teufelaudio/mynd-hardware/PCB_Schematics/KiCad/Jack_USB/ALTIUM_EMBEDDED_MODELS/SCM7060.step

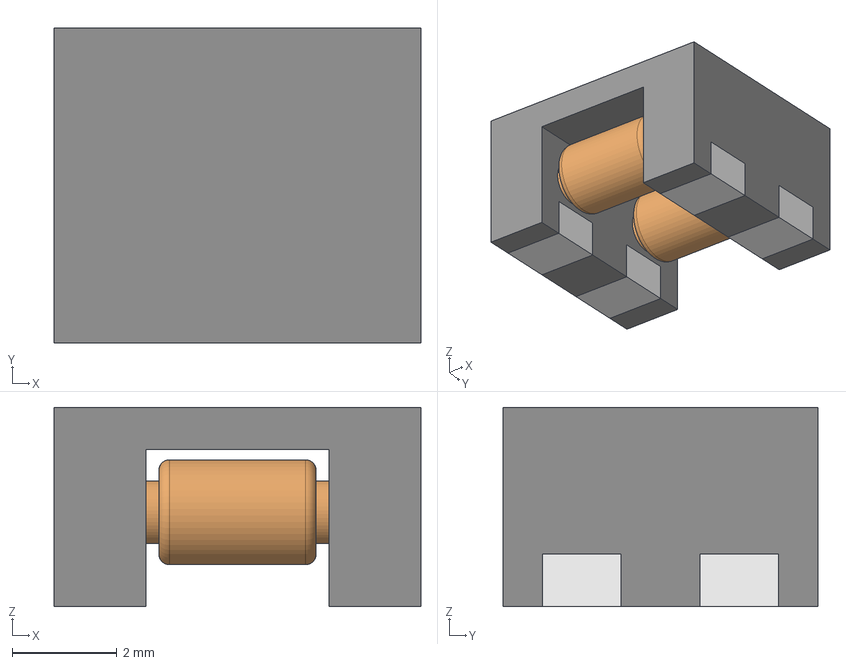
[picture p15: CAD file, 2025-11-21]
PCB_Schematics/KiCad/Jack_USB/ALTIUM_EMBEDDED_MODELS/SCM7060.step
7.00 x 6.00 x 3.80 mm
PIN001
PIN002
PIN003
PIN004
