teufelaudio/mynd-hardware/PCB_Schematics/Altium/Main/ALTIUM_EMBEDDED_MODELS/User Library-RESC1005X___.step

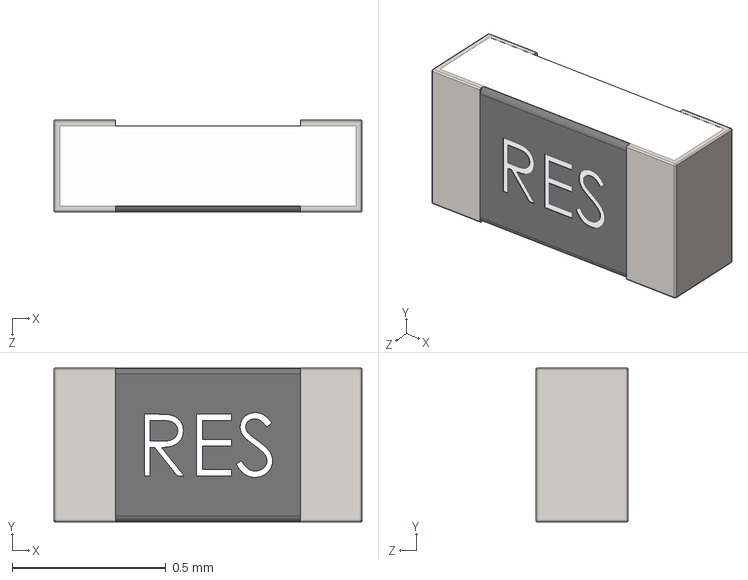
[picture p16: CAD file, 2025-11-21]
PCB_Schematics/Altium/Main/ALTIUM_EMBEDDED_MODELS/User Library-RESC1005X___.step
1.00 x 0.5 x 0.3 mm
