teufelaudio/mynd-hardware/PCB_Schematics/KiCad/Amp/ALTIUM_EMBEDDED_MODELS/RHB0032E.stp

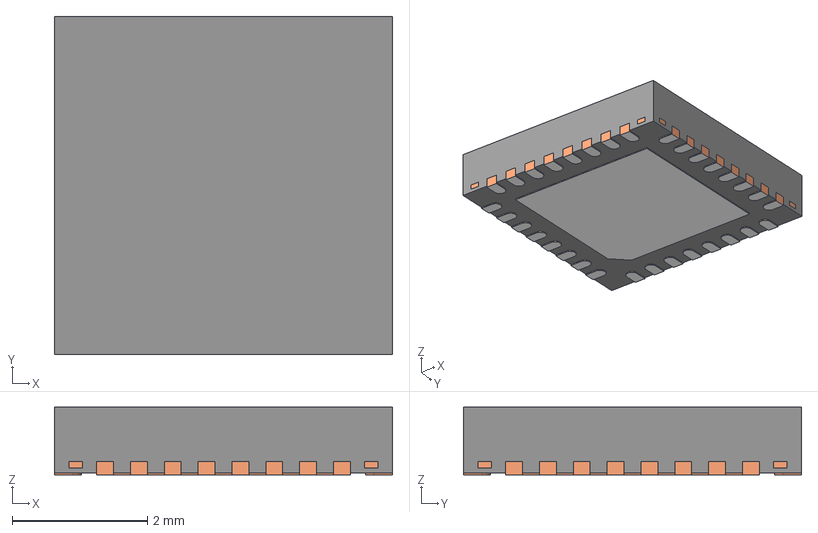
[picture p17: CAD file, 2025-11-21]
PCB_Schematics/KiCad/Amp/ALTIUM_EMBEDDED_MODELS/RHB0032E.stp
5.00 x 5.00 x 1.00 mm
BODY-QFN
FRAME-RHB0032E
PIN1-ID
