teufelaudio/mynd-hardware/PCB_Schematics/KiCad/Bluetooth/ALTIUM_EMBEDDED_MODELS/WB2835P.step

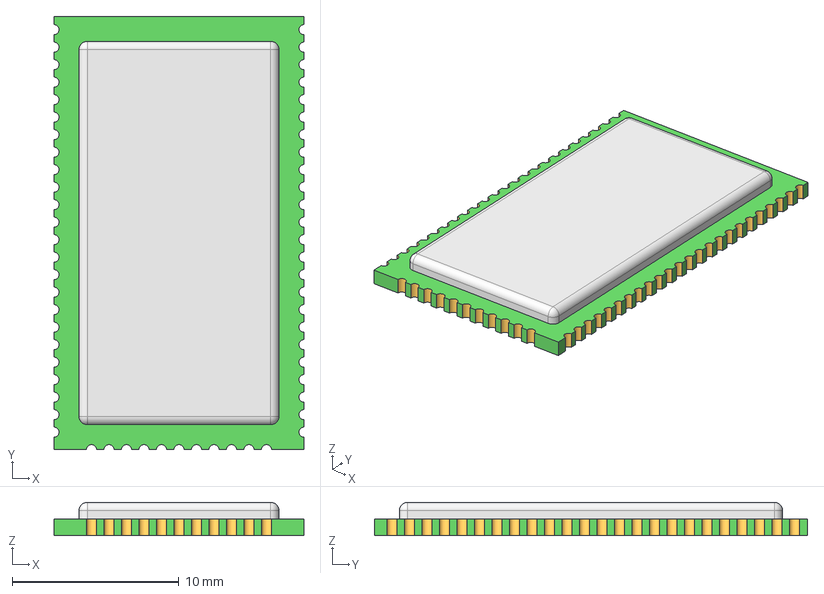
[picture p18: CAD file, 2025-11-21]
PCB_Schematics/KiCad/Bluetooth/ALTIUM_EMBEDDED_MODELS/WB2835P.step
15.0 x 26.0 x 2.00 mm
