teufelaudio/mynd-hardware/PCB_Schematics/KiCad/Jack_USB/ALTIUM_EMBEDDED_MODELS/K3D-DX07WH24JA3-V2_JAE_Proprietary.STEP

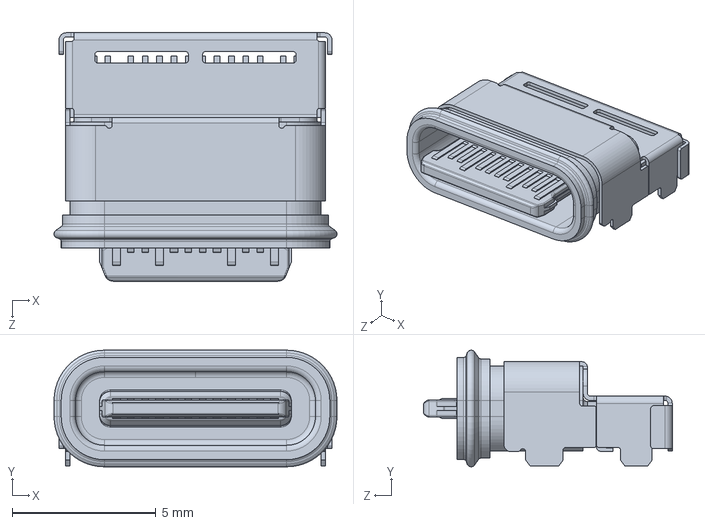
[picture p19: CAD file, 2025-11-21]
PCB_Schematics/KiCad/Jack_USB/ALTIUM_EMBEDDED_MODELS/K3D-DX07WH24JA3-V2_JAE_Proprietary.STEP
9.85 x 4.06 x 8.65 mm
