teufelaudio/mynd-hardware/PCB_Schematics/KiCad/Main/ALTIUM_EMBEDDED_MODELS/User Library-RESC3216X___.step

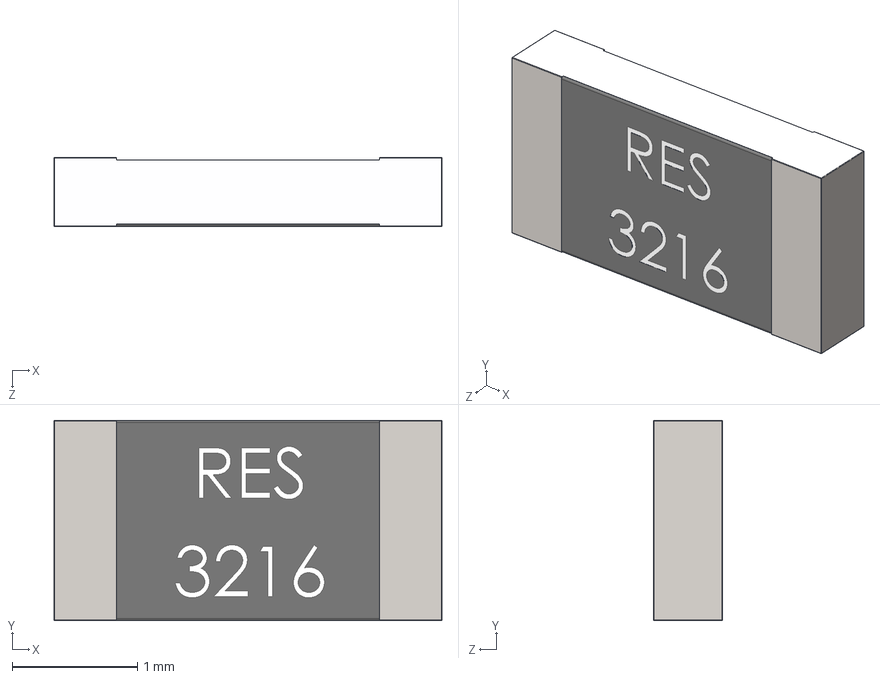
[picture p20: CAD file, 2025-11-21]
PCB_Schematics/KiCad/Main/ALTIUM_EMBEDDED_MODELS/User Library-RESC3216X___.step
3.10 x 1.60 x 0.55 mm
