teufelaudio/mynd-hardware/PCB_Schematics/Altium/Main/ALTIUM_EMBEDDED_MODELS/0805_145.step

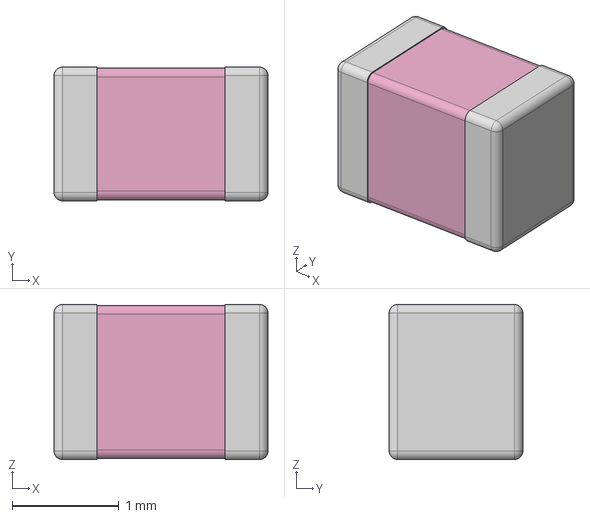
[picture p21: CAD file, 2025-11-21]
PCB_Schematics/Altium/Main/ALTIUM_EMBEDDED_MODELS/0805_145.step
2.00 x 1.25 x 1.45 mm
