teufelaudio/mynd-hardware/PCB_Schematics/KiCad/Amp/ALTIUM_EMBEDDED_MODELS/User Library-CAPC3216X___.step

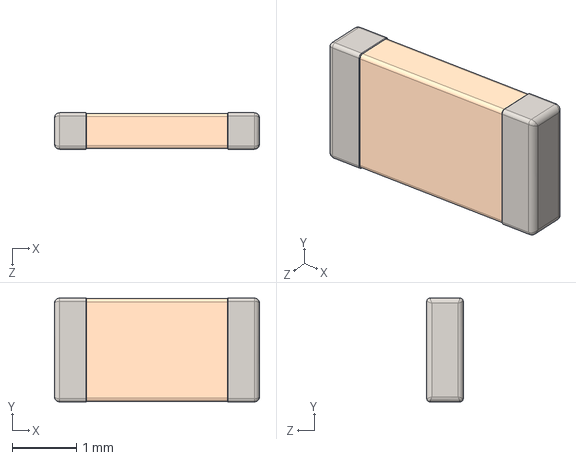
[picture p22: CAD file, 2025-11-21]
PCB_Schematics/KiCad/Amp/ALTIUM_EMBEDDED_MODELS/User Library-CAPC3216X___.step
3.20 x 1.62 x 0.57 mm
