teufelaudio/mynd-hardware/PCB_Schematics/KiCad/Bluetooth/ALTIUM_EMBEDDED_MODELS/User Library-RESC2012X___.STEP

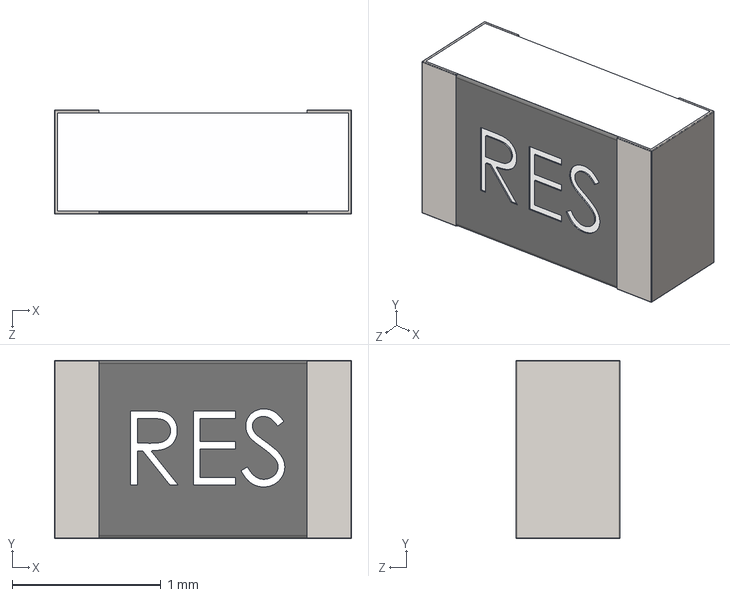
[picture p23: CAD file, 2025-11-21]
PCB_Schematics/KiCad/Bluetooth/ALTIUM_EMBEDDED_MODELS/User Library-RESC2012X___.STEP
2.00 x 1.20 x 0.7 mm
