teufelaudio/mynd-hardware/PCB_Schematics/KiCad/Main/ALTIUM_EMBEDDED_MODELS/pin_header_a-sl127-dg-g10mp1.stp

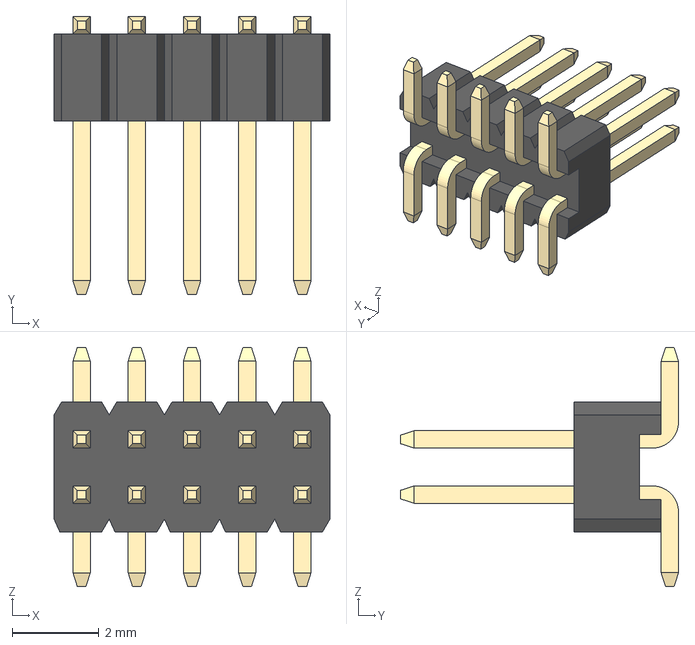
[picture p24: CAD file, 2025-11-21]
PCB_Schematics/KiCad/Main/ALTIUM_EMBEDDED_MODELS/pin_header_a-sl127-dg-g10mp1.stp
6.35 x 6.40 x 5.50 mm
