teufelaudio/mynd-hardware/PCB_Schematics/Altium/Main/ALTIUM_EMBEDDED_MODELS/DBV0003A.stp

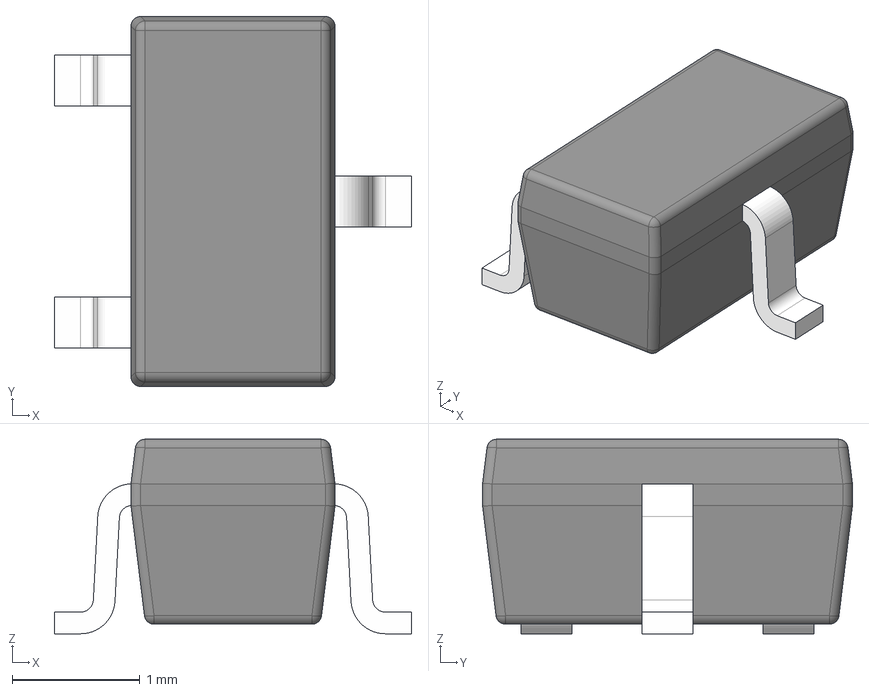
[picture p25: CAD file, 2025-11-21]
PCB_Schematics/Altium/Main/ALTIUM_EMBEDDED_MODELS/DBV0003A.stp
2.80 x 2.90 x 1.52 mm
LEAD x 3
