teufelaudio/mynd-hardware/PCB_Schematics/KiCad/Amp/ALTIUM_EMBEDDED_MODELS/User Library-RESC1608X___.STEP

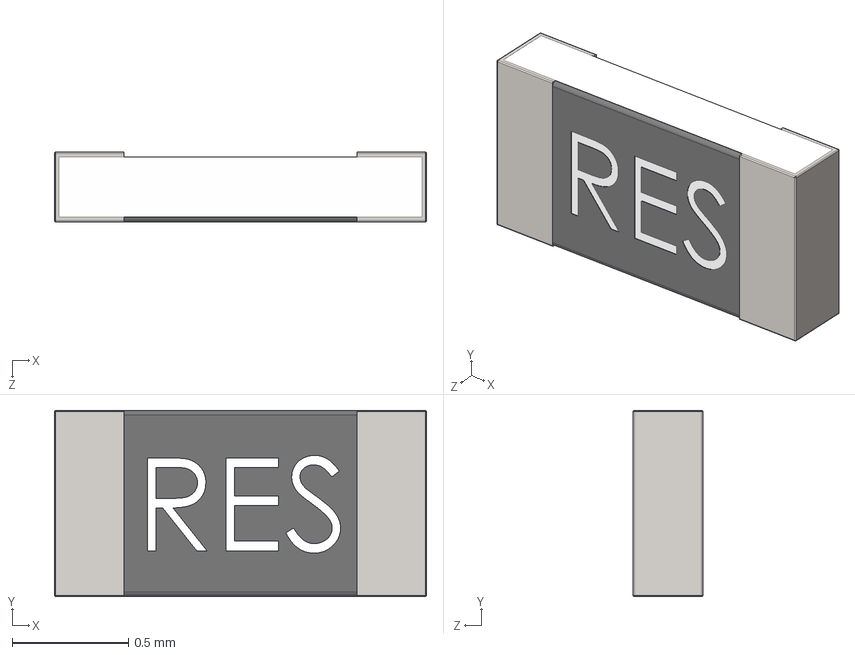
[picture p26: CAD file, 2025-11-21]
PCB_Schematics/KiCad/Amp/ALTIUM_EMBEDDED_MODELS/User Library-RESC1608X___.STEP
1.60 x 0.8 x 0.3 mm
