teufelaudio/mynd-hardware/PCB_Schematics/KiCad/Bluetooth/ALTIUM_EMBEDDED_MODELS/User Library-IPEX.STEP

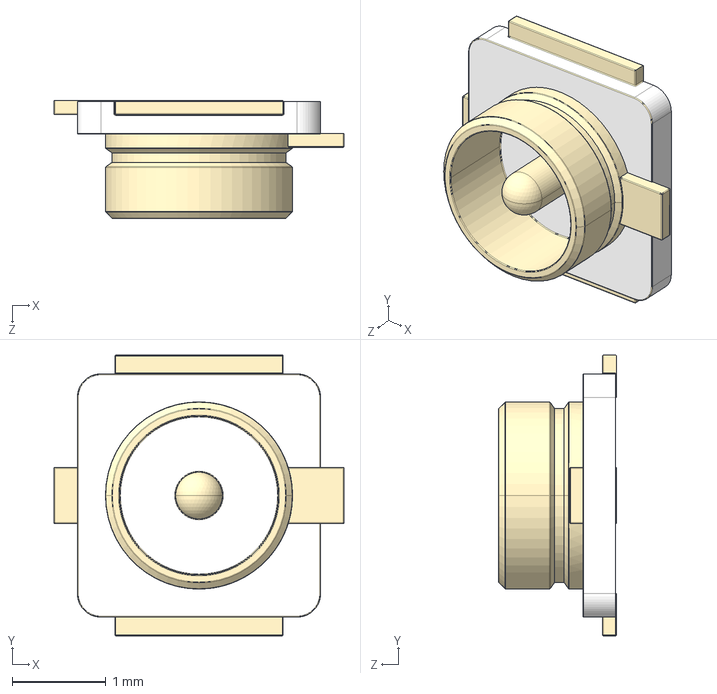
[picture p27: CAD file, 2025-11-21]
PCB_Schematics/KiCad/Bluetooth/ALTIUM_EMBEDDED_MODELS/User Library-IPEX.STEP
3.10 x 3.00 x 1.26 mm
