teufelaudio/mynd-hardware/PCB_Schematics/KiCad/Main/ALTIUM_EMBEDDED_MODELS/RSN0032B.stp

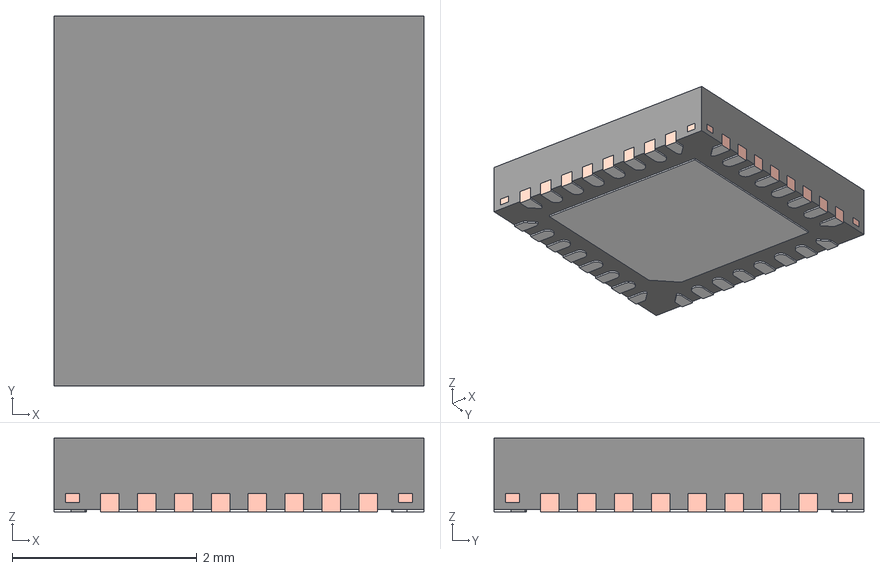
[picture p28: CAD file, 2025-11-21]
PCB_Schematics/KiCad/Main/ALTIUM_EMBEDDED_MODELS/RSN0032B.stp
4.00 x 4.00 x 0.8 mm
BODY-QFN
FRAME-RSN0032B
PIN1-ID
