teufelaudio/mynd-hardware/PCB_Schematics/KiCad/Bluetooth/ALTIUM_EMBEDDED_MODELS/pin_header_a-sl254-eg-g03mr1.stp

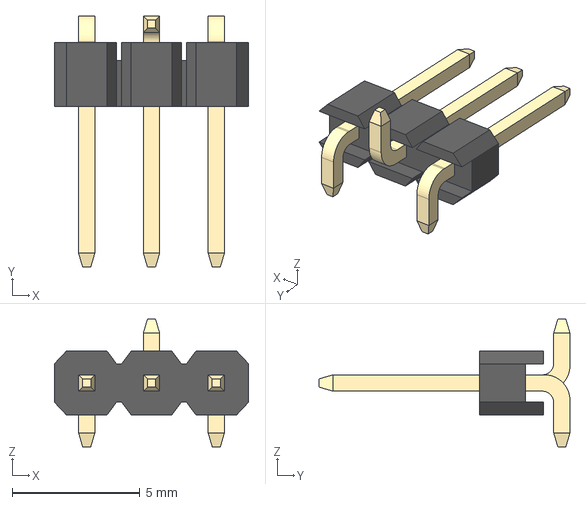
[picture p29: CAD file, 2025-11-21]
PCB_Schematics/KiCad/Bluetooth/ALTIUM_EMBEDDED_MODELS/pin_header_a-sl254-eg-g03mr1.stp
7.62 x 9.84 x 5.00 mm
