teufelaudio/mynd-hardware/PCB_Schematics/KiCad/Jack_USB/ALTIUM_EMBEDDED_MODELS/User Library-SOD-123FL CASE 498.STEP

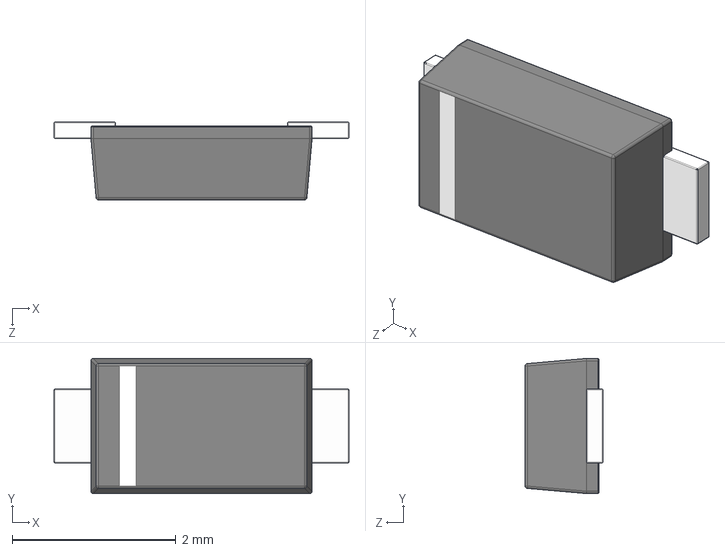
[picture p30: CAD file, 2025-11-21]
PCB_Schematics/KiCad/Jack_USB/ALTIUM_EMBEDDED_MODELS/User Library-SOD-123FL CASE 498.STEP
3.60 x 1.65 x 0.951 mm
