teufelaudio/mynd-hardware/PCB_Schematics/KiCad/Main/ALTIUM_EMBEDDED_MODELS/User Library-INDC2012X___.step

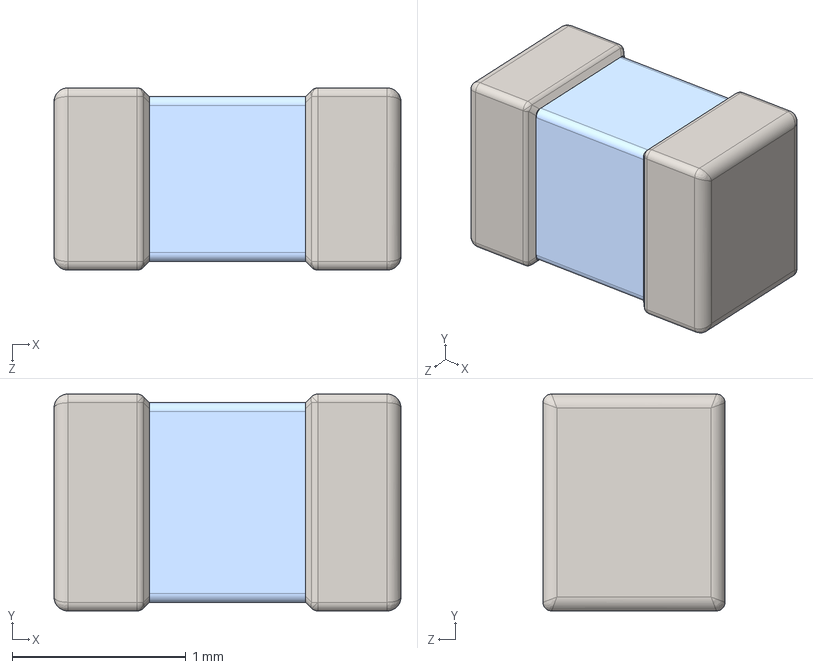
[picture p31: CAD file, 2025-11-21]
PCB_Schematics/KiCad/Main/ALTIUM_EMBEDDED_MODELS/User Library-INDC2012X___.step
2.00 x 1.25 x 1.05 mm
