teufelaudio/mynd-hardware/PCB_Schematics/KiCad/UI/ALTIUM_EMBEDDED_MODELS/RGE0024F.stp

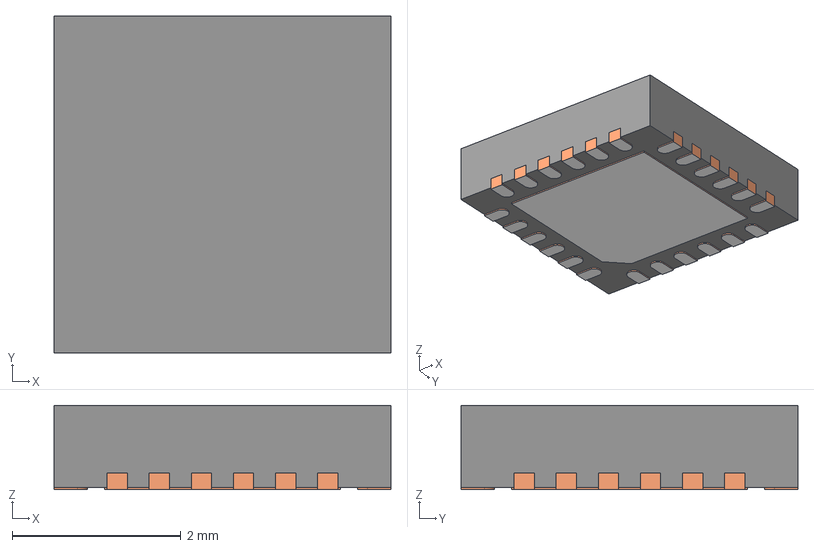
[picture p32: CAD file, 2025-11-21]
PCB_Schematics/KiCad/UI/ALTIUM_EMBEDDED_MODELS/RGE0024F.stp
4.00 x 4.00 x 1.00 mm
BODY-QFN
FRAME-RGE0024F
PIN1-ID
