teufelaudio/mynd-hardware/PCB_Schematics/KiCad/Amp/ALTIUM_EMBEDDED_MODELS/8x10_Chip.stp

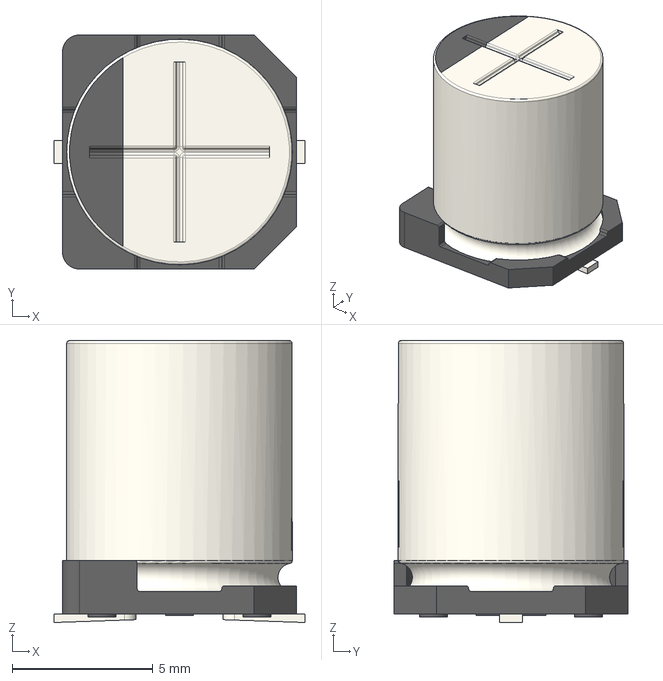
[picture p33: CAD file, 2025-11-21]
PCB_Schematics/KiCad/Amp/ALTIUM_EMBEDDED_MODELS/8x10_Chip.stp
8.90 x 8.30 x 10.0 mm
