teufelaudio/mynd-hardware/PCB_Schematics/KiCad/Jack_USB/ALTIUM_EMBEDDED_MODELS/0603_80.step

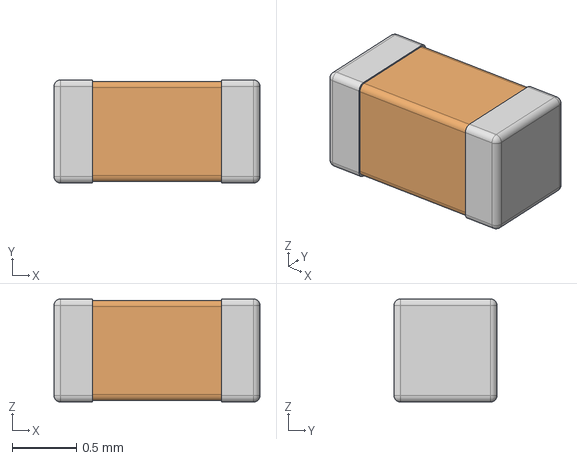
[picture p34: CAD file, 2025-11-21]
PCB_Schematics/KiCad/Jack_USB/ALTIUM_EMBEDDED_MODELS/0603_80.step
1.60 x 0.8 x 0.8 mm
