teufelaudio/mynd-hardware/PCB_Schematics/KiCad/Main/ALTIUM_EMBEDDED_MODELS/SNR6020B.step

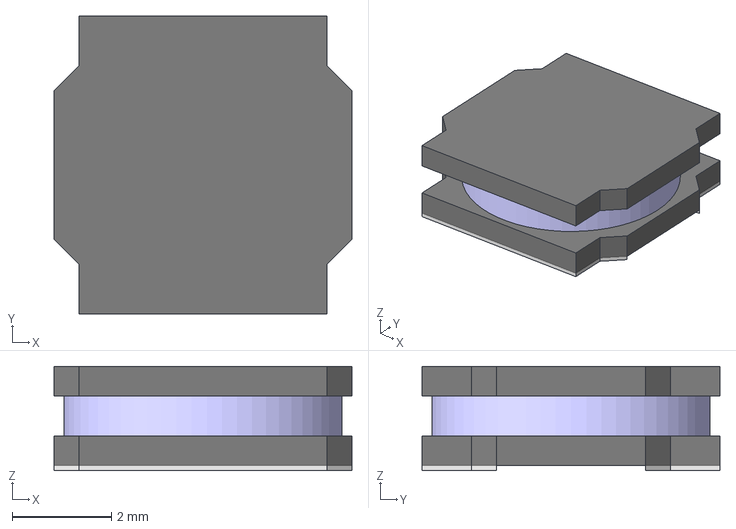
[picture p35: CAD file, 2025-11-21]
PCB_Schematics/KiCad/Main/ALTIUM_EMBEDDED_MODELS/SNR6020B.step
6.00 x 6.00 x 2.10 mm
