teufelaudio/mynd-hardware/PCB_Schematics/Altium/Main/ALTIUM_EMBEDDED_MODELS/LQFP64_1000X1000X160_50.step

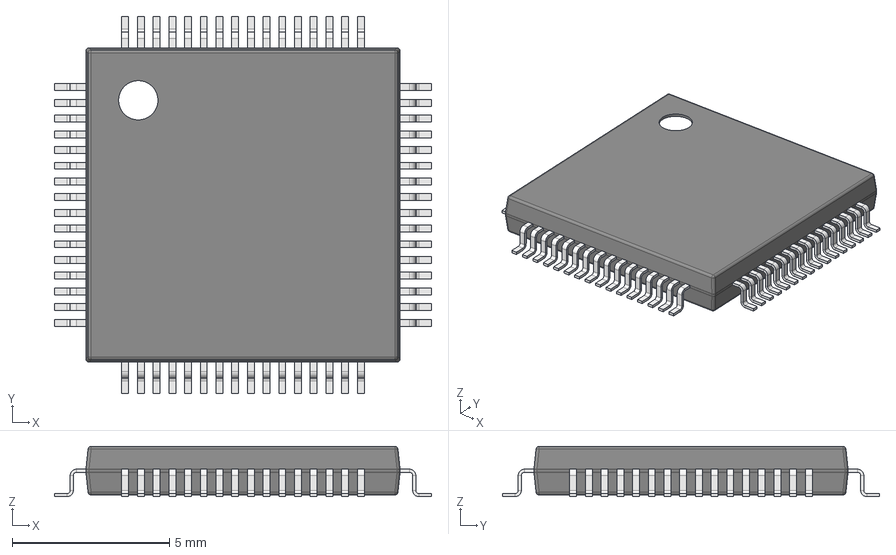
[picture p36: CAD file, 2025-11-21]
PCB_Schematics/Altium/Main/ALTIUM_EMBEDDED_MODELS/LQFP64_1000X1000X160_50.step
12.0 x 12.0 x 1.60 mm
Leader x 64
