teufelaudio/mynd-hardware/PCB_Schematics/KiCad/Amp/ALTIUM_EMBEDDED_MODELS/0603_105.step

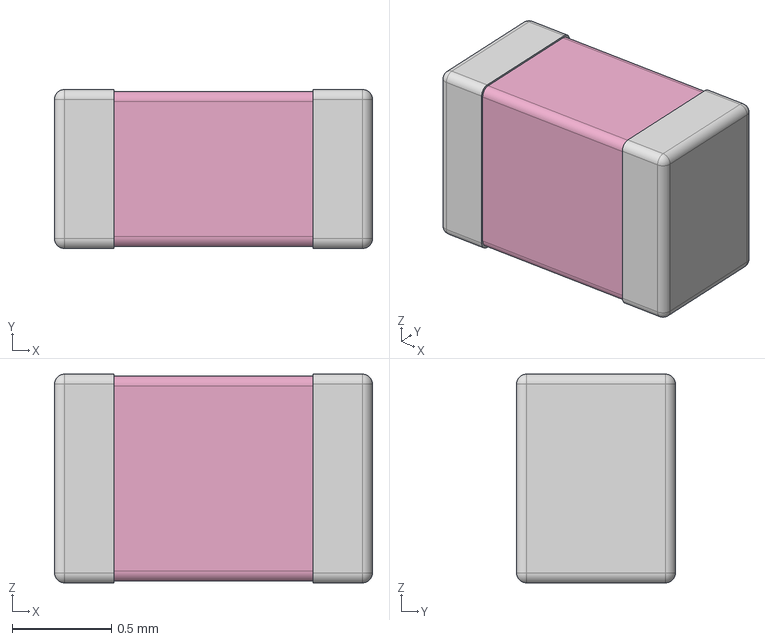
[picture p37: CAD file, 2025-11-21]
PCB_Schematics/KiCad/Amp/ALTIUM_EMBEDDED_MODELS/0603_105.step
1.60 x 0.8 x 1.05 mm
