teufelaudio/mynd-hardware/PCB_Schematics/Altium/Main/ALTIUM_EMBEDDED_MODELS/User Library-ALU-G.STEP

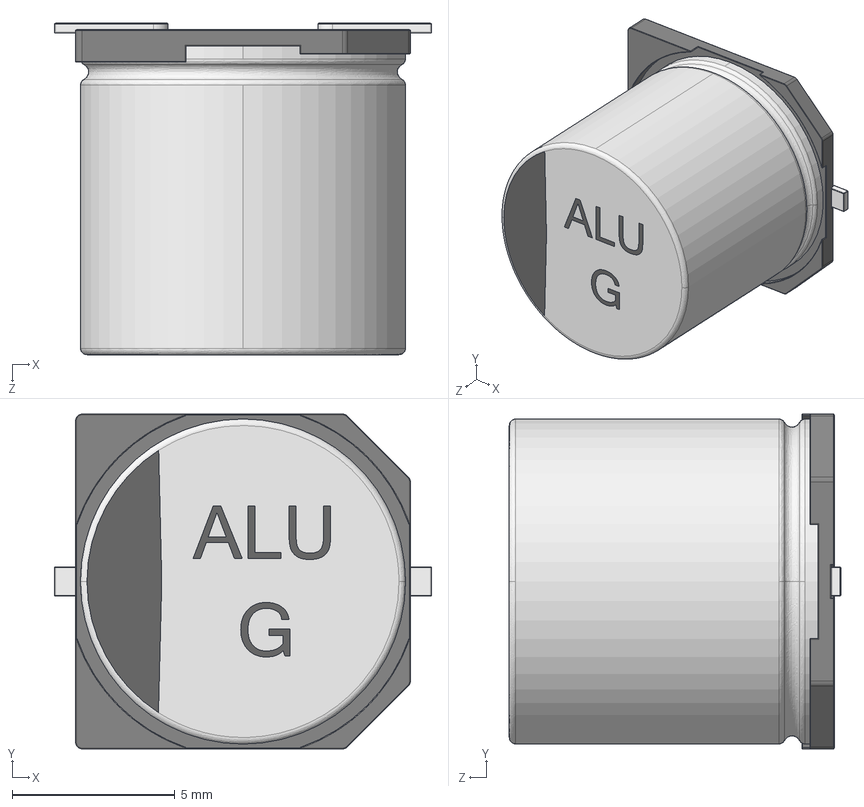
[picture p38: CAD file, 2025-11-21]
PCB_Schematics/Altium/Main/ALTIUM_EMBEDDED_MODELS/User Library-ALU-G.STEP
11.6 x 10.3 x 10.2 mm
User Library-ALU-G_Pins_1
User Library-ALU-G_Fuss_1
User Library-ALU-G_K_X_F6rper_1
User Library-ALU-G_Beschriftung_1
