teufelaudio/mynd-hardware/PCB_Schematics/KiCad/Bluetooth/ALTIUM_EMBEDDED_MODELS/SOP127P600-8N.step

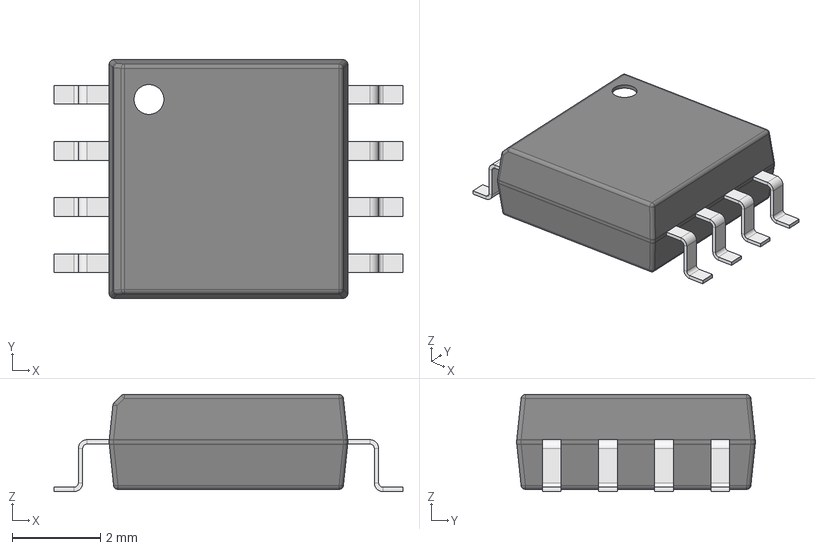
[picture p40: CAD file, 2025-11-21]
PCB_Schematics/KiCad/Bluetooth/ALTIUM_EMBEDDED_MODELS/SOP127P600-8N.step
7.90 x 5.40 x 2.20 mm
Leader x 8
