teufelaudio/mynd-hardware/PCB_Schematics/KiCad/Bluetooth/ALTIUM_EMBEDDED_MODELS/User Library-CAPC1005X___.step

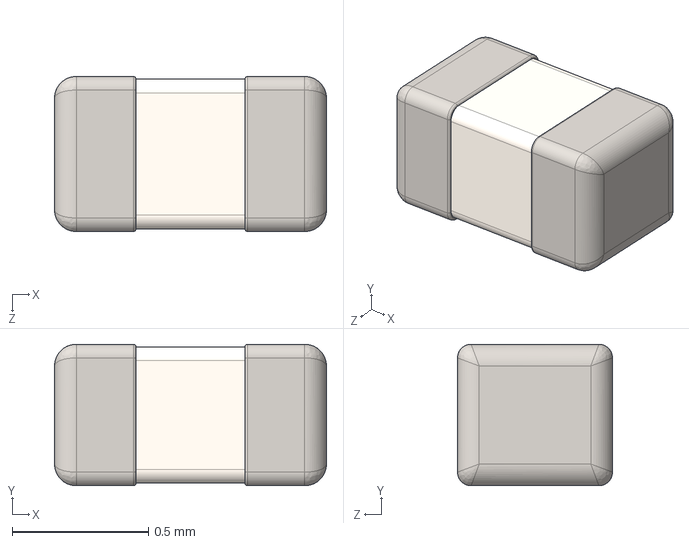
[picture p41: CAD file, 2025-11-21]
PCB_Schematics/KiCad/Bluetooth/ALTIUM_EMBEDDED_MODELS/User Library-CAPC1005X___.step
1.00 x 0.52 x 0.57 mm
