teufelaudio/mynd-hardware/PCB_Schematics/KiCad/Bluetooth/ALTIUM_EMBEDDED_MODELS/User Library-SOT-23-5.STEP

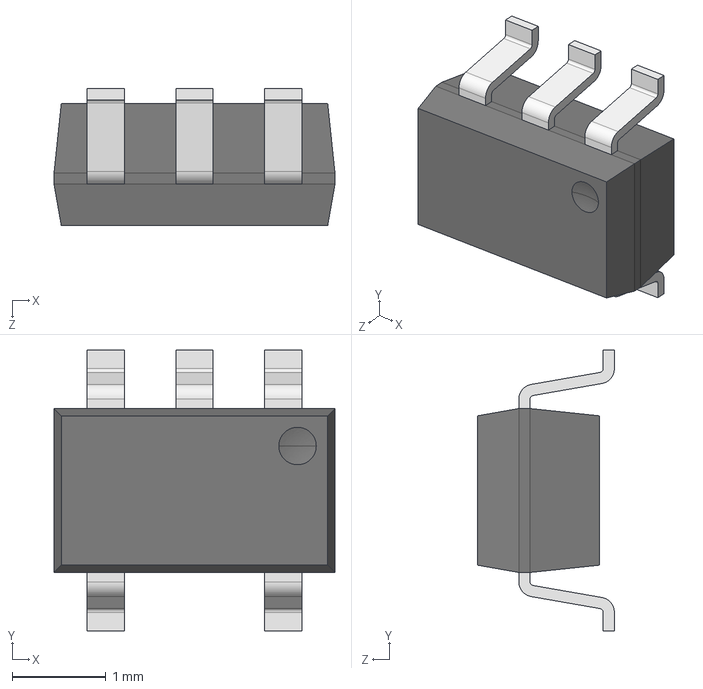
[picture p43: CAD file, 2025-11-21]
PCB_Schematics/KiCad/Bluetooth/ALTIUM_EMBEDDED_MODELS/User Library-SOT-23-5.STEP
3.00 x 3.00 x 1.46 mm
User Library-SOT-23-5_pin_SOT_sot-23-6_1 x 5
User Library-SOT-23-5_body_sot23-6_1
