teufelaudio/mynd-hardware/PCB_Schematics/KiCad/UI/ALTIUM_EMBEDDED_MODELS/LED_RGB_1608.step

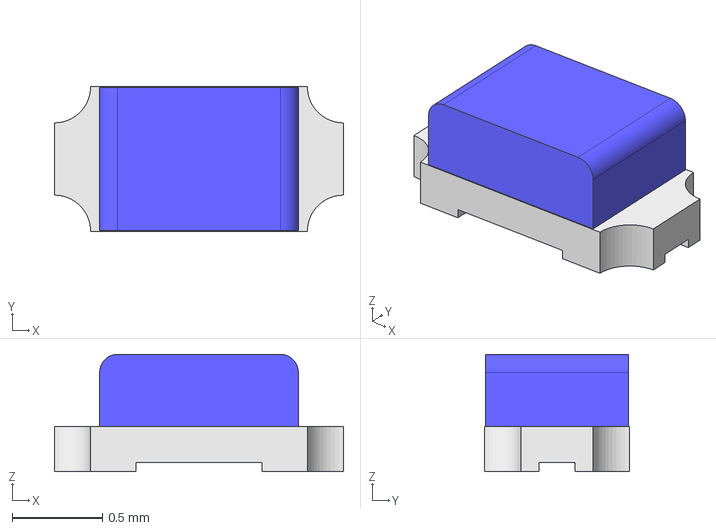
[picture p44: CAD file, 2025-11-21]
PCB_Schematics/KiCad/UI/ALTIUM_EMBEDDED_MODELS/LED_RGB_1608.step
1.60 x 0.8 x 0.65 mm
