teufelaudio/mynd-hardware/PCB_Schematics/KiCad/Amp/ALTIUM_EMBEDDED_MODELS/JSHC0650.step

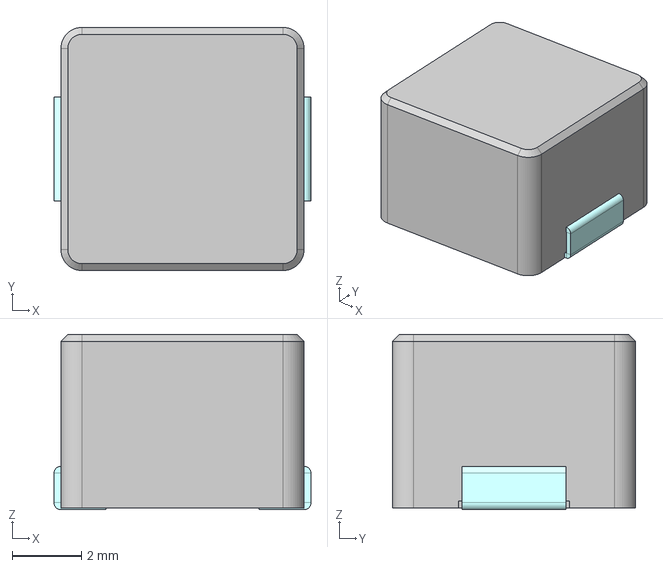
[picture p45: CAD file, 2025-11-21]
PCB_Schematics/KiCad/Amp/ALTIUM_EMBEDDED_MODELS/JSHC0650.step
7.40 x 7.00 x 5.05 mm
PIN
