teufelaudio/mynd-hardware/PCB_Schematics/KiCad/Main/ALTIUM_EMBEDDED_MODELS/phb-row-st-smt-2-3p.stp

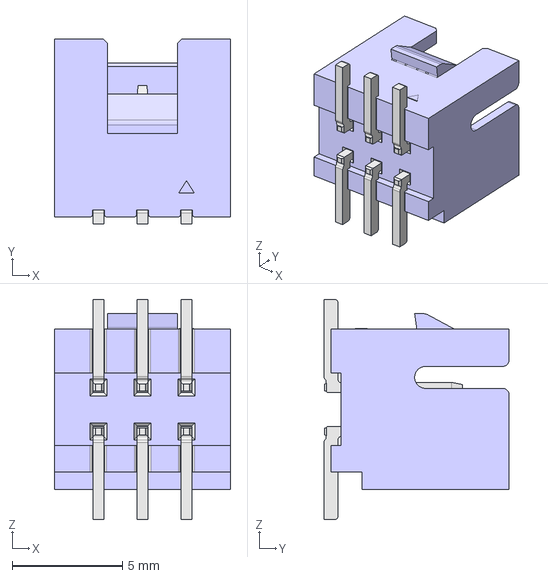
[picture p46: CAD file, 2025-11-21]
PCB_Schematics/KiCad/Main/ALTIUM_EMBEDDED_MODELS/phb-row-st-smt-2-3p.stp
8.00 x 8.43 x 10.0 mm
