teufelaudio/mynd-hardware/PCB_Schematics/Altium/Main/ALTIUM_EMBEDDED_MODELS/JSHC1040.step

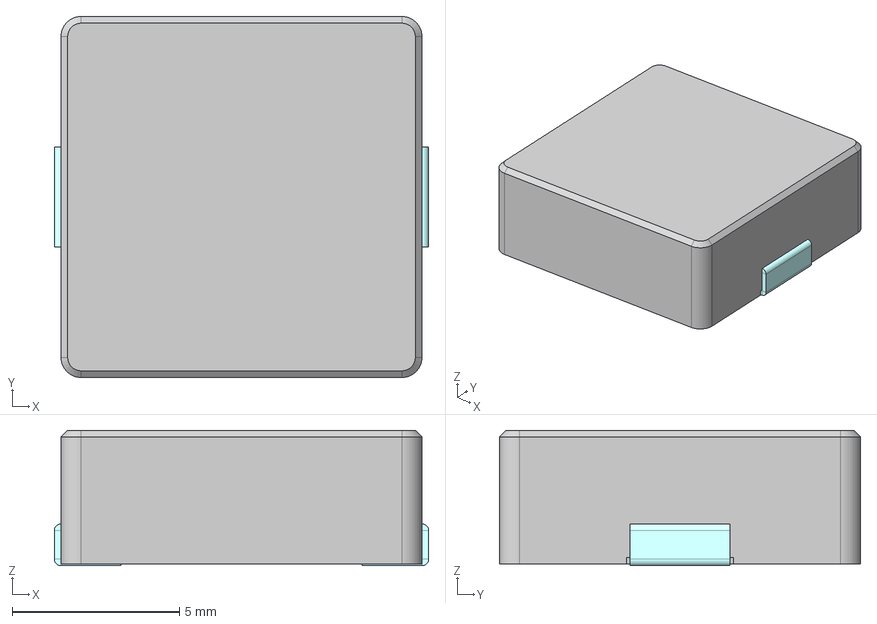
[picture p47: CAD file, 2025-11-21]
PCB_Schematics/Altium/Main/ALTIUM_EMBEDDED_MODELS/JSHC1040.step
11.2 x 10.8 x 4.05 mm
PIN
