teufelaudio/mynd-hardware/PCB_Schematics/KiCad/Amp/ALTIUM_EMBEDDED_MODELS/JSHC0630.step

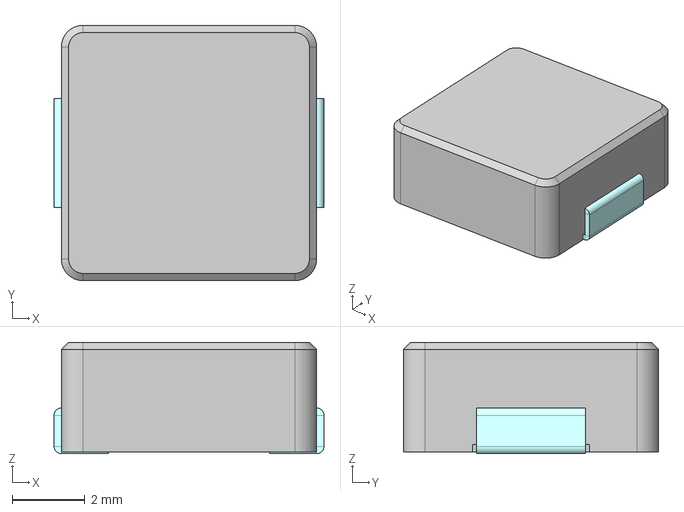
[picture p48: CAD file, 2025-11-21]
PCB_Schematics/KiCad/Amp/ALTIUM_EMBEDDED_MODELS/JSHC0630.step
7.40 x 7.00 x 3.05 mm
PIN
