teufelaudio/mynd-hardware/PCB_Schematics/KiCad/Amp/ALTIUM_EMBEDDED_MODELS/10x10_Chip.stp

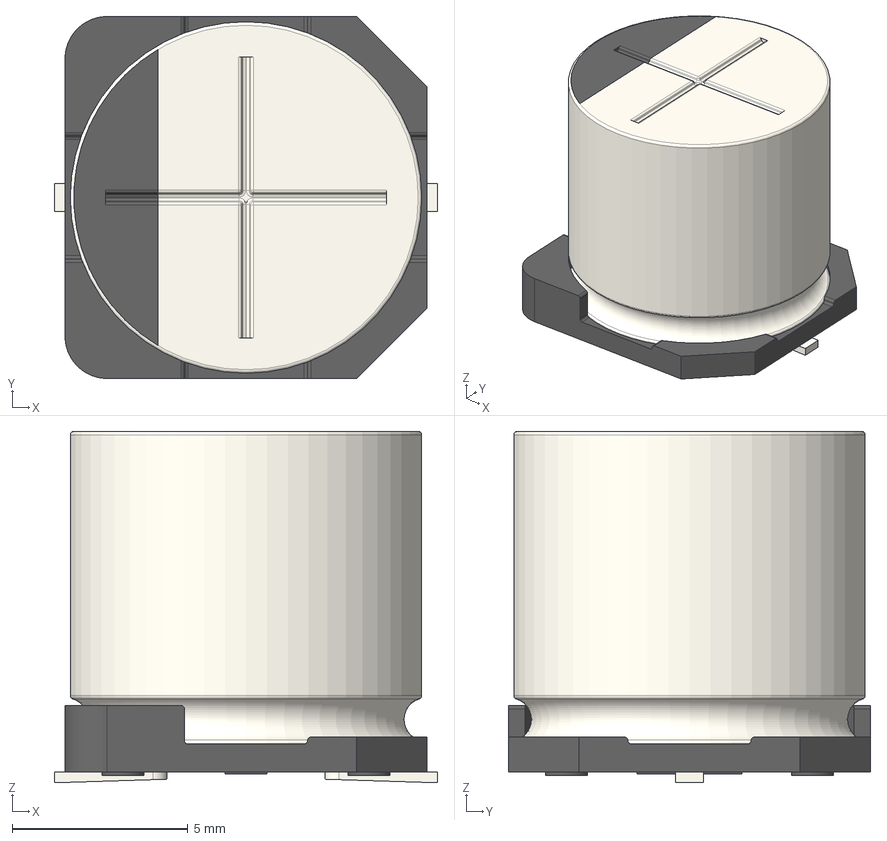
[picture p50: CAD file, 2025-11-21]
PCB_Schematics/KiCad/Amp/ALTIUM_EMBEDDED_MODELS/10x10_Chip.stp
10.9 x 10.3 x 10.0 mm
