teufelaudio/mynd-hardware/PCB_Schematics/KiCad/Main/ALTIUM_EMBEDDED_MODELS/TMPA1206.step

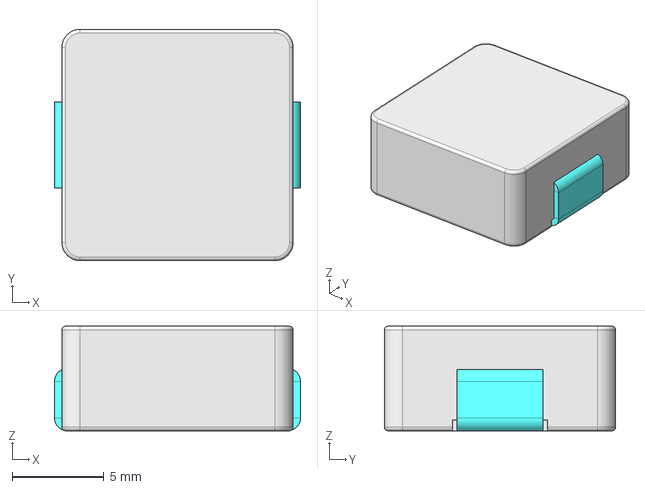
[picture p51: CAD file, 2025-11-21]
PCB_Schematics/KiCad/Main/ALTIUM_EMBEDDED_MODELS/TMPA1206.step
13.4 x 12.6 x 5.70 mm
Pin
