teufelaudio/mynd-hardware/PCB_Schematics/Altium/Main/ALTIUM_EMBEDDED_MODELS/User Library-SOT457.STEP

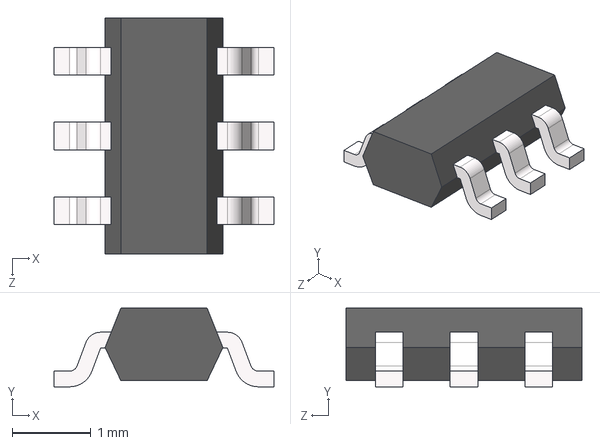
[picture p52: CAD file, 2025-11-21]
PCB_Schematics/Altium/Main/ALTIUM_EMBEDDED_MODELS/User Library-SOT457.STEP
2.80 x 1.00 x 3.00 mm
User Library-SOT457_body
User Library-SOT457_pin x 6
