teufelaudio/mynd-hardware/PCB_Schematics/KiCad/Main/ALTIUM_EMBEDDED_MODELS/RSW0010A.stp

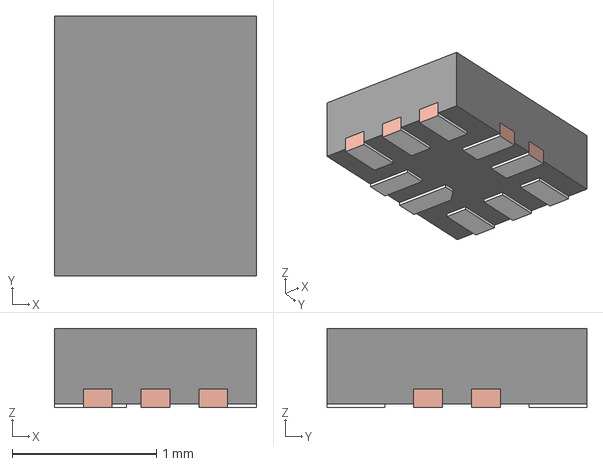
[picture p53: CAD file, 2025-11-21]
PCB_Schematics/KiCad/Main/ALTIUM_EMBEDDED_MODELS/RSW0010A.stp
1.40 x 1.80 x 0.55 mm
FRAME
