teufelaudio/mynd-hardware/PCB_Schematics/Altium/Main/ALTIUM_EMBEDDED_MODELS/User Library-SOD-123_DiodesInc.STEP

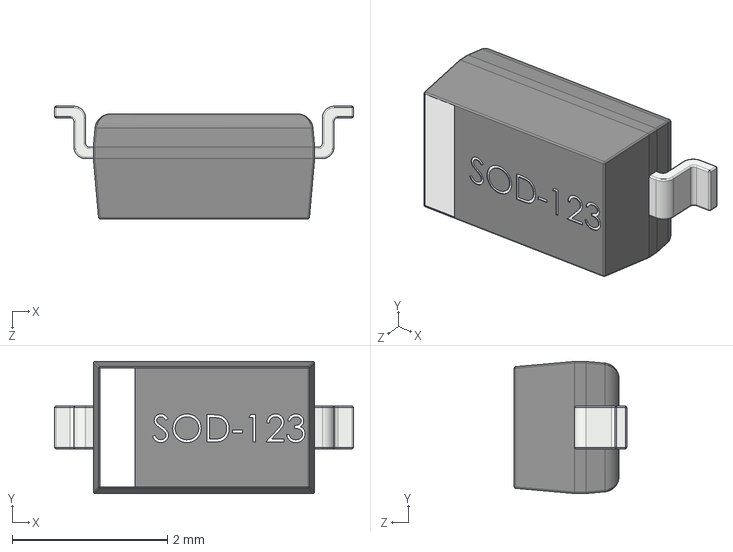
[picture p54: CAD file, 2025-11-21]
PCB_Schematics/Altium/Main/ALTIUM_EMBEDDED_MODELS/User Library-SOD-123_DiodesInc.STEP
3.85 x 1.70 x 1.45 mm
