teufelaudio/mynd-hardware/PCB_Schematics/KiCad/Main/ALTIUM_EMBEDDED_MODELS/RGR0020A.stp

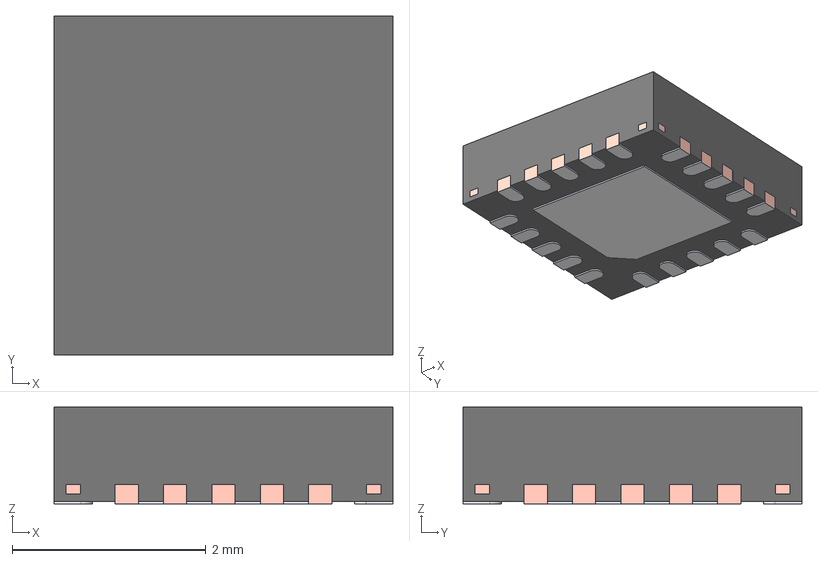
[picture p56: CAD file, 2025-11-21]
PCB_Schematics/KiCad/Main/ALTIUM_EMBEDDED_MODELS/RGR0020A.stp
3.50 x 3.50 x 1.00 mm
FRAME
PIN1_AREA
