teufelaudio/mynd-hardware/PCB_Schematics/Altium/Main/ALTIUM_EMBEDDED_MODELS/20-wtb-a-double-row-st-smt-2x5p(1).stp

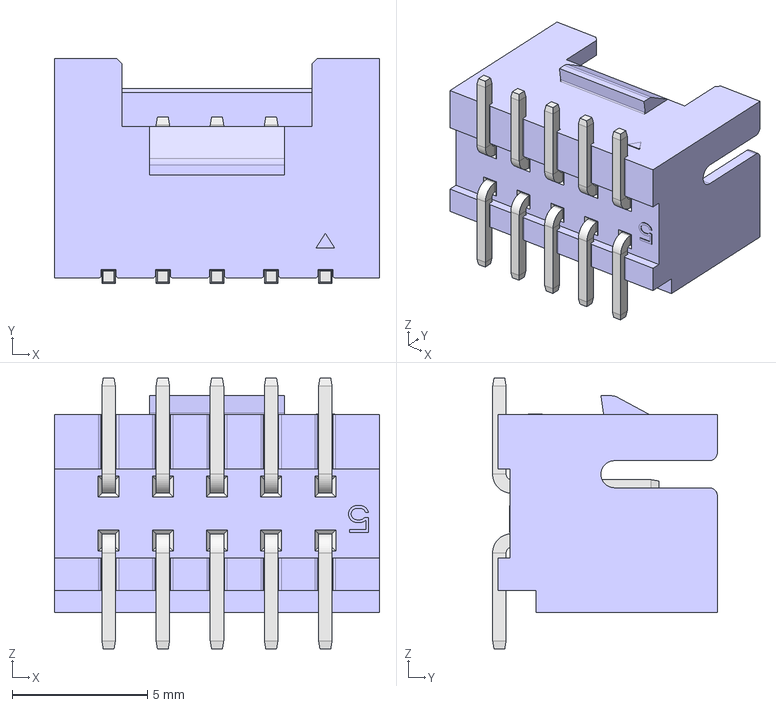
[picture p57: CAD file, 2025-11-21]
PCB_Schematics/Altium/Main/ALTIUM_EMBEDDED_MODELS/20-wtb-a-double-row-st-smt-2x5p(1).stp
12.0 x 8.30 x 10.0 mm
