teufelaudio/mynd-hardware/PCB_Schematics/KiCad/Main/ALTIUM_EMBEDDED_MODELS/DGK0008A.stp

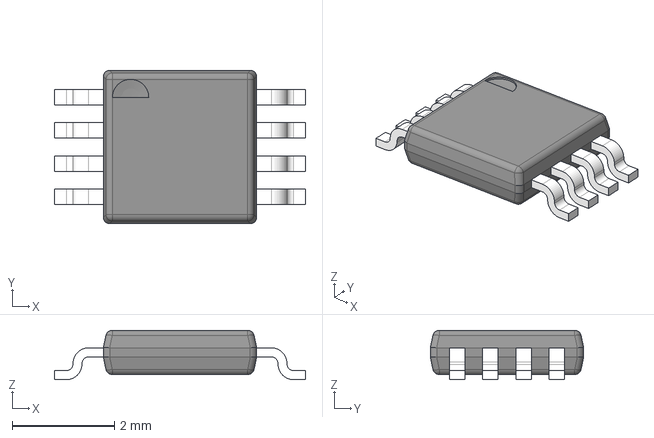
[picture p58: CAD file, 2025-11-21]
PCB_Schematics/KiCad/Main/ALTIUM_EMBEDDED_MODELS/DGK0008A.stp
4.90 x 3.00 x 0.965 mm
BODY_MUA08A
LEAD_MUA08A x 8
