teufelaudio/mynd-hardware/PCB_Schematics/Altium/Main/ALTIUM_EMBEDDED_MODELS/6.3x5.4_Chip.stp

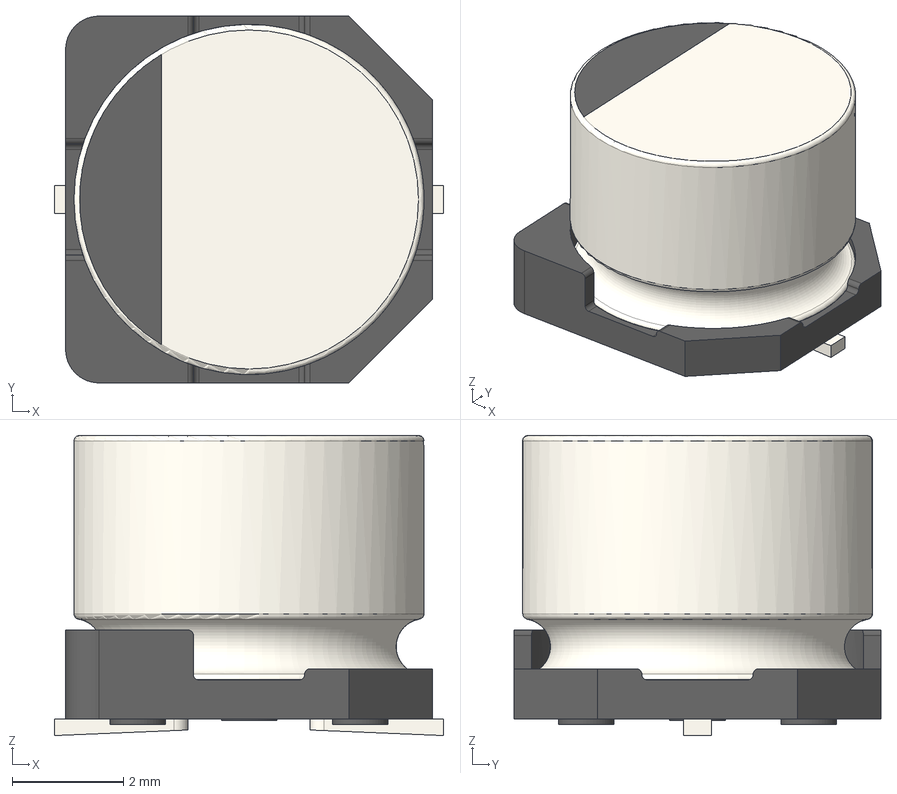
[picture p59: CAD file, 2025-11-21]
PCB_Schematics/Altium/Main/ALTIUM_EMBEDDED_MODELS/6.3x5.4_Chip.stp
7.00 x 6.60 x 5.40 mm
