teufelaudio/mynd-hardware/PCB_Schematics/PDF/Mynd_Main_SCH.PDF

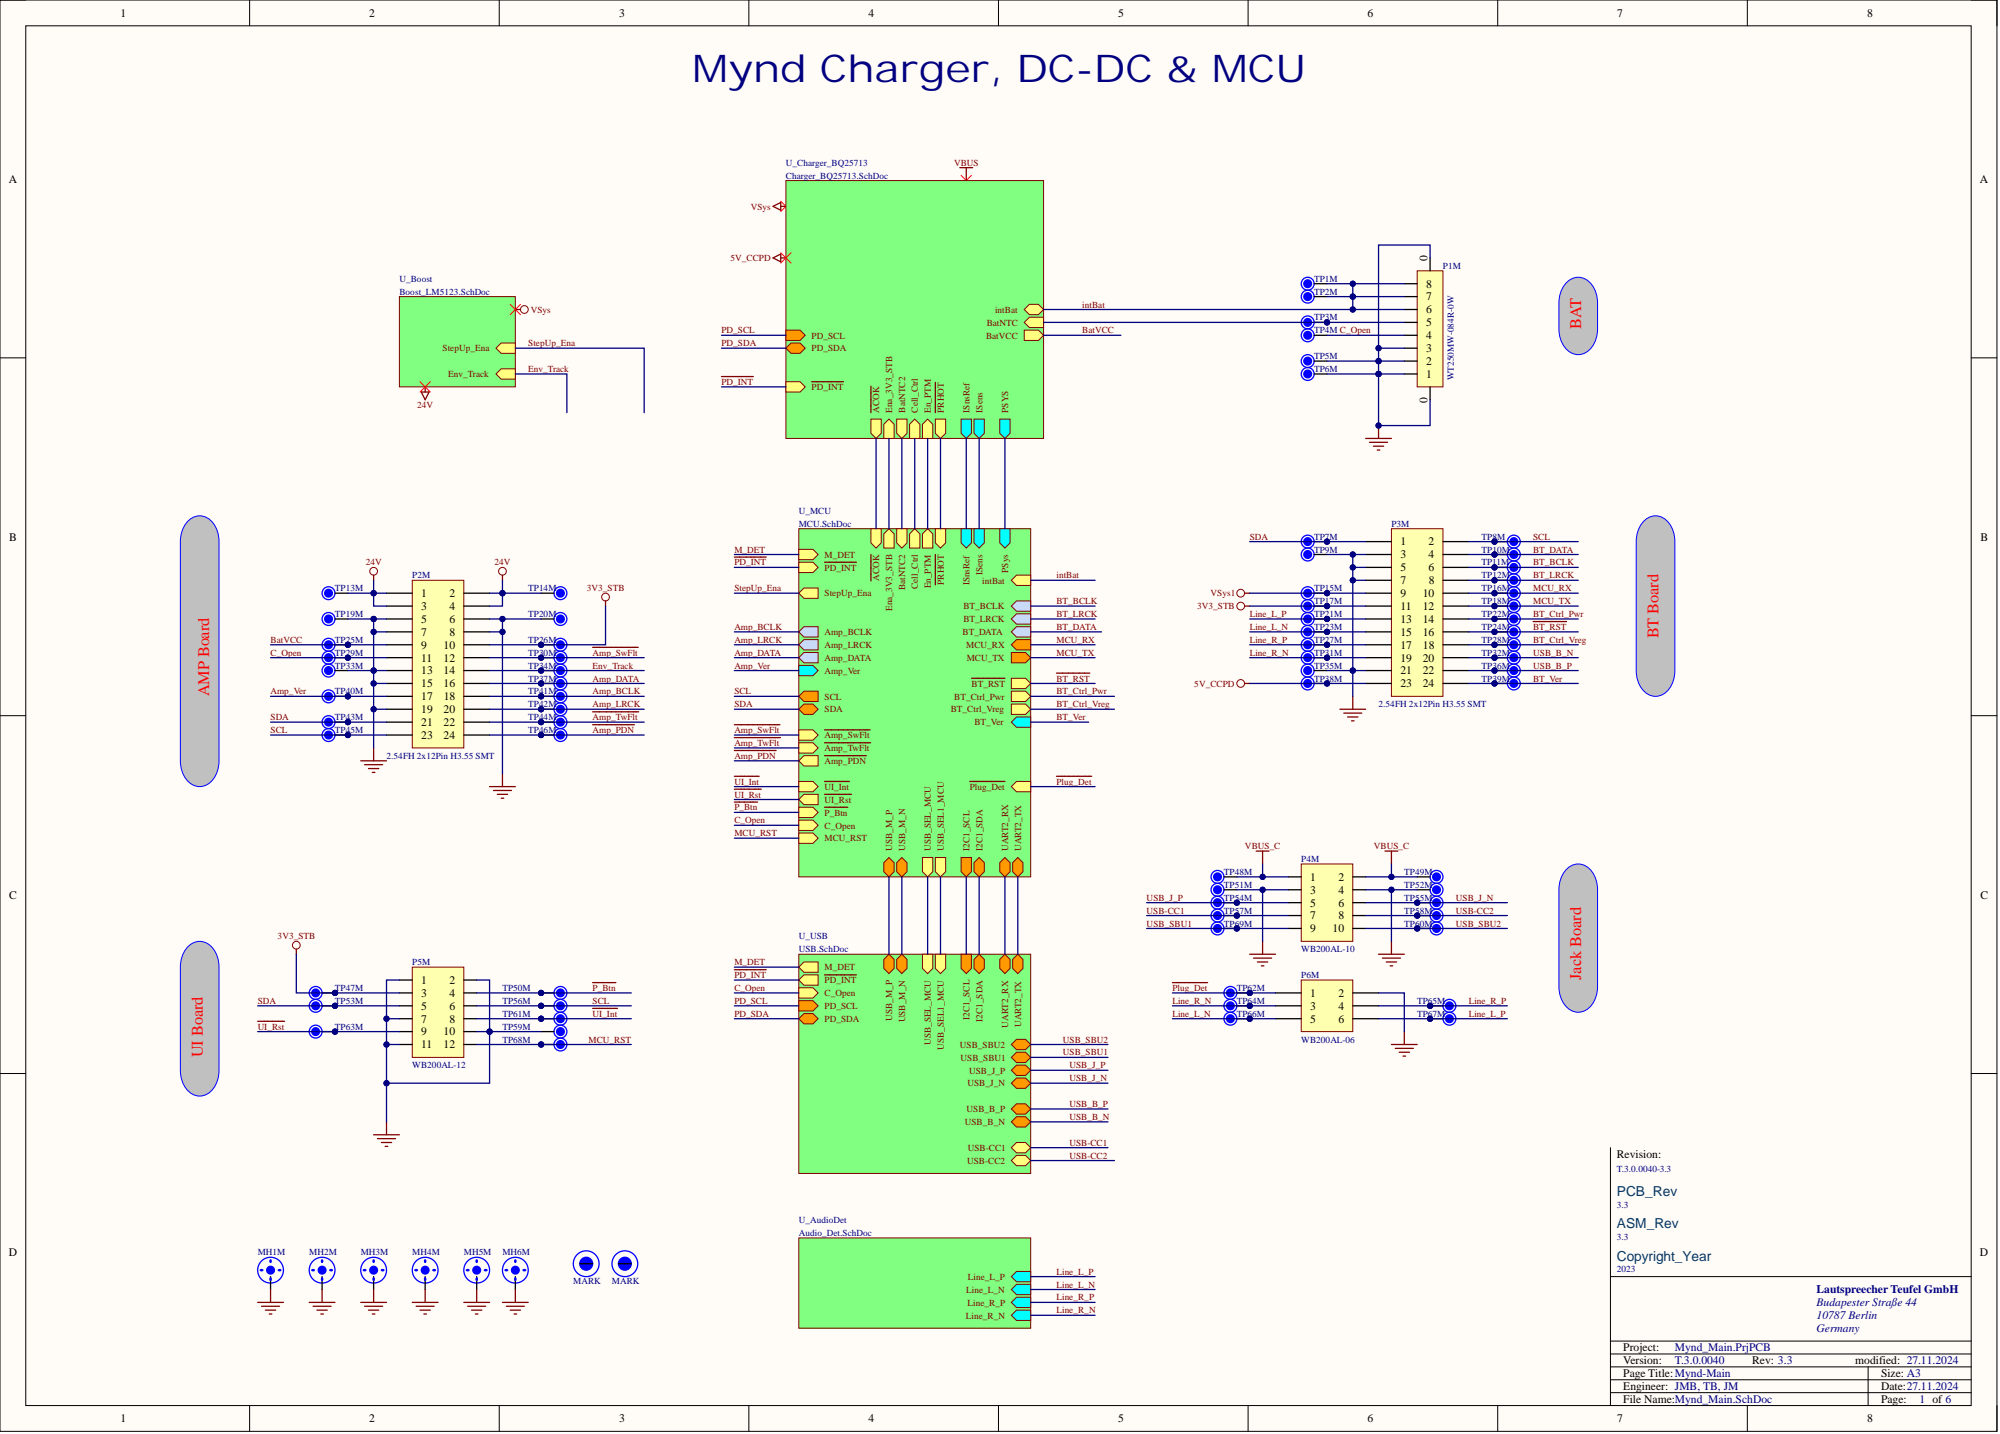
[picture p61: page 1]

Mynd Charger, DC-DC & MCU

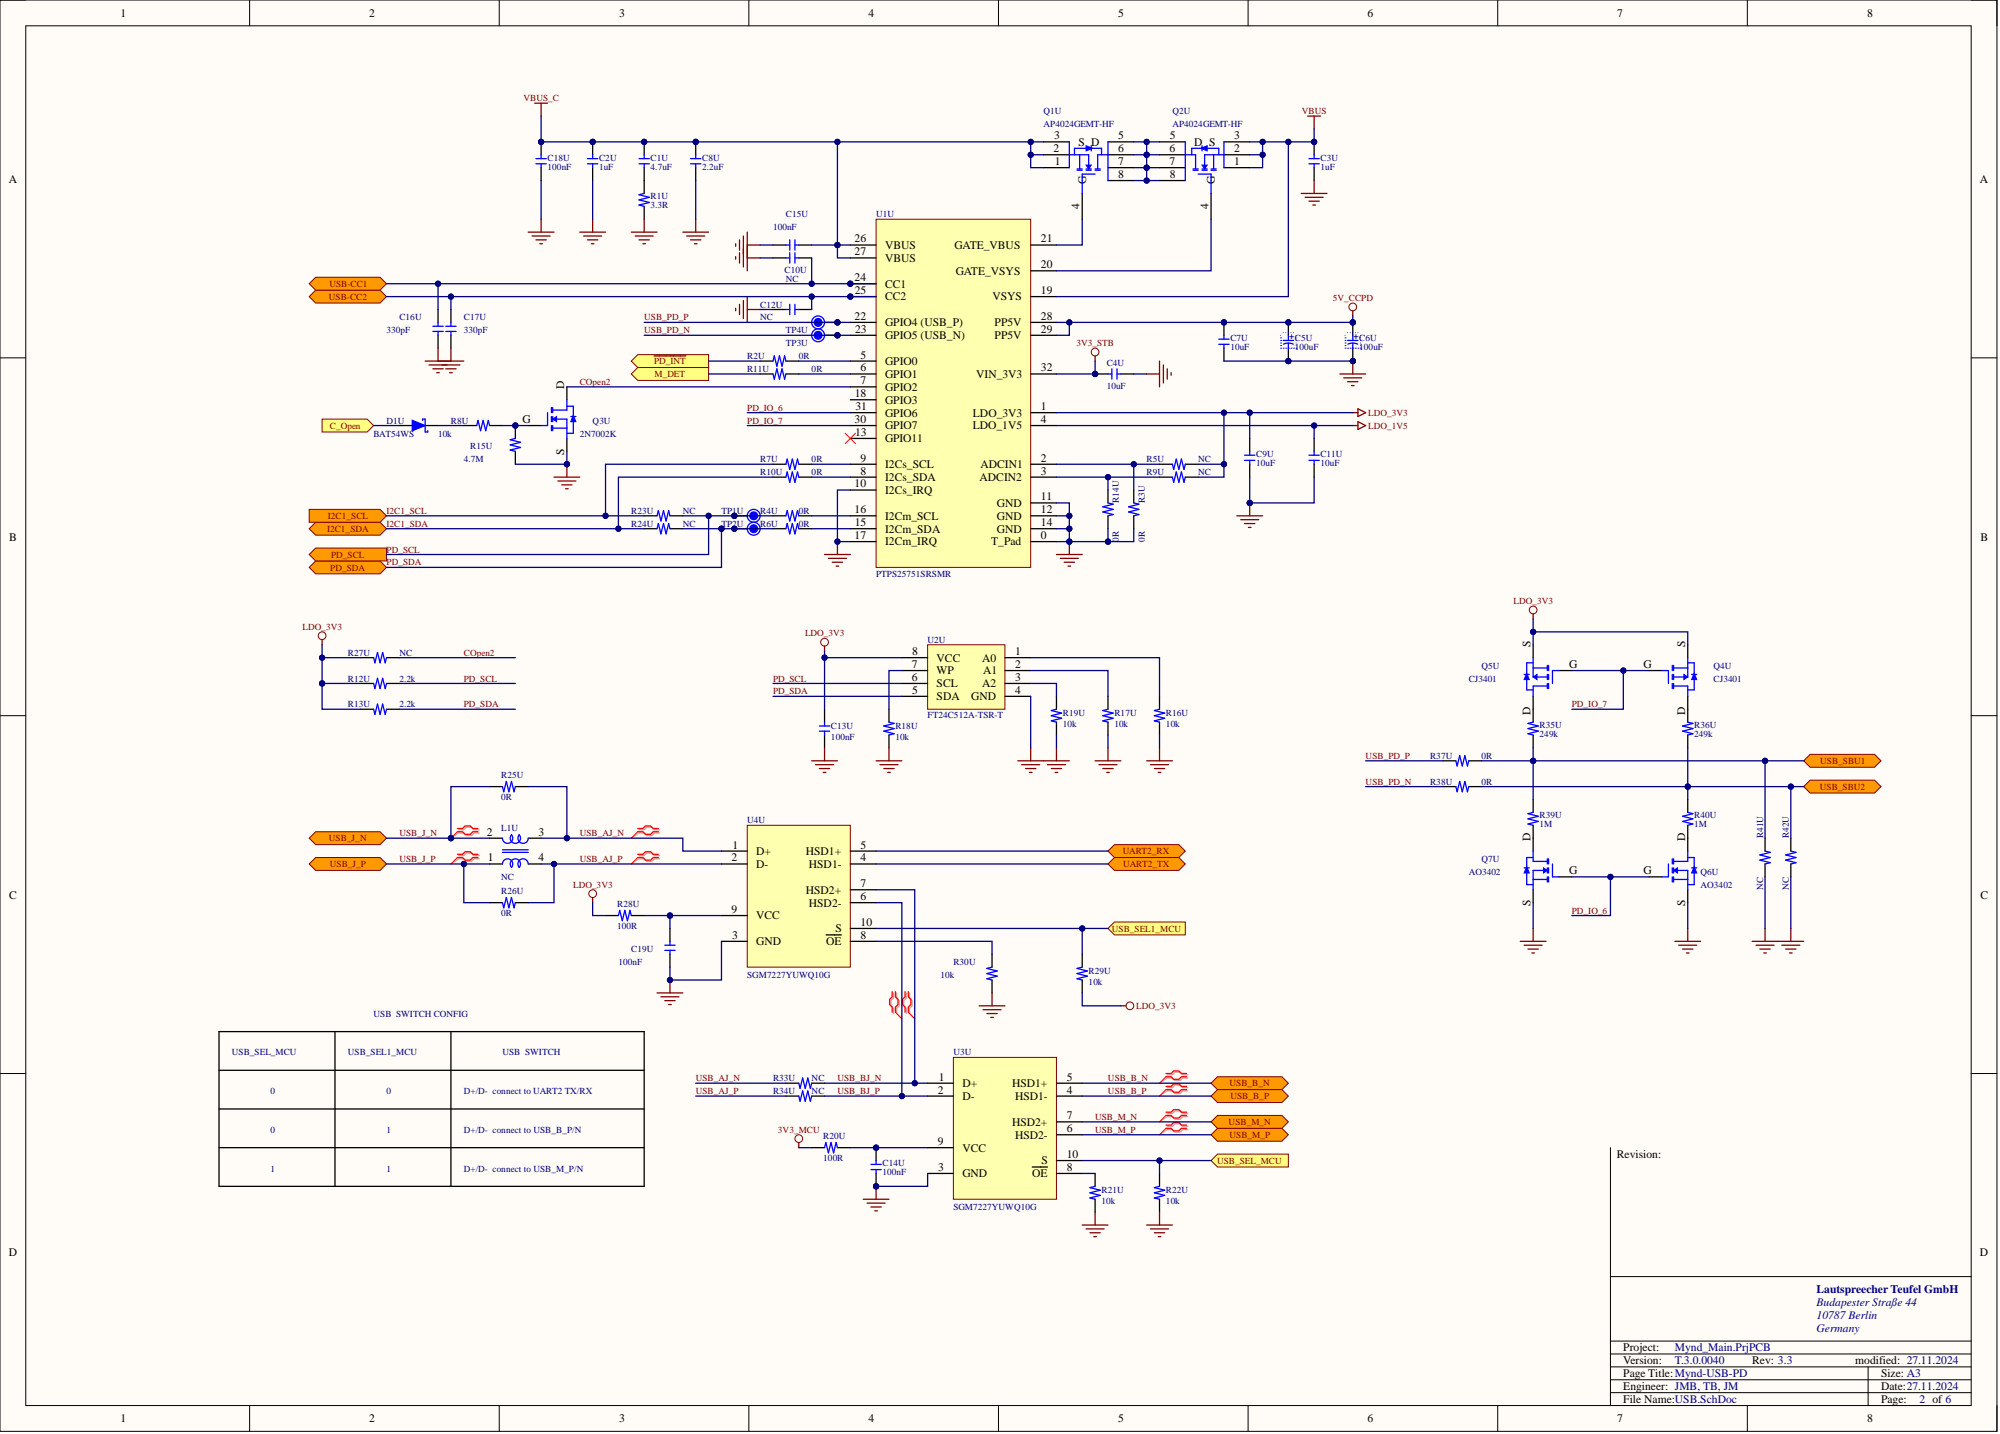
[picture p62: page 2]

USB_PD_P | GPIO4 (USB_P) 22

I2Cm_SCL 16

PD_SCL | | I2Cm_IRQ 17

USB_SEL_MCU | USB_SEL1_MCU | USB SWITCH

0 | 0 | D+/D- connect to UART2 TX/RX

0 | 1 | D+/D- connect to USB_B_P/N

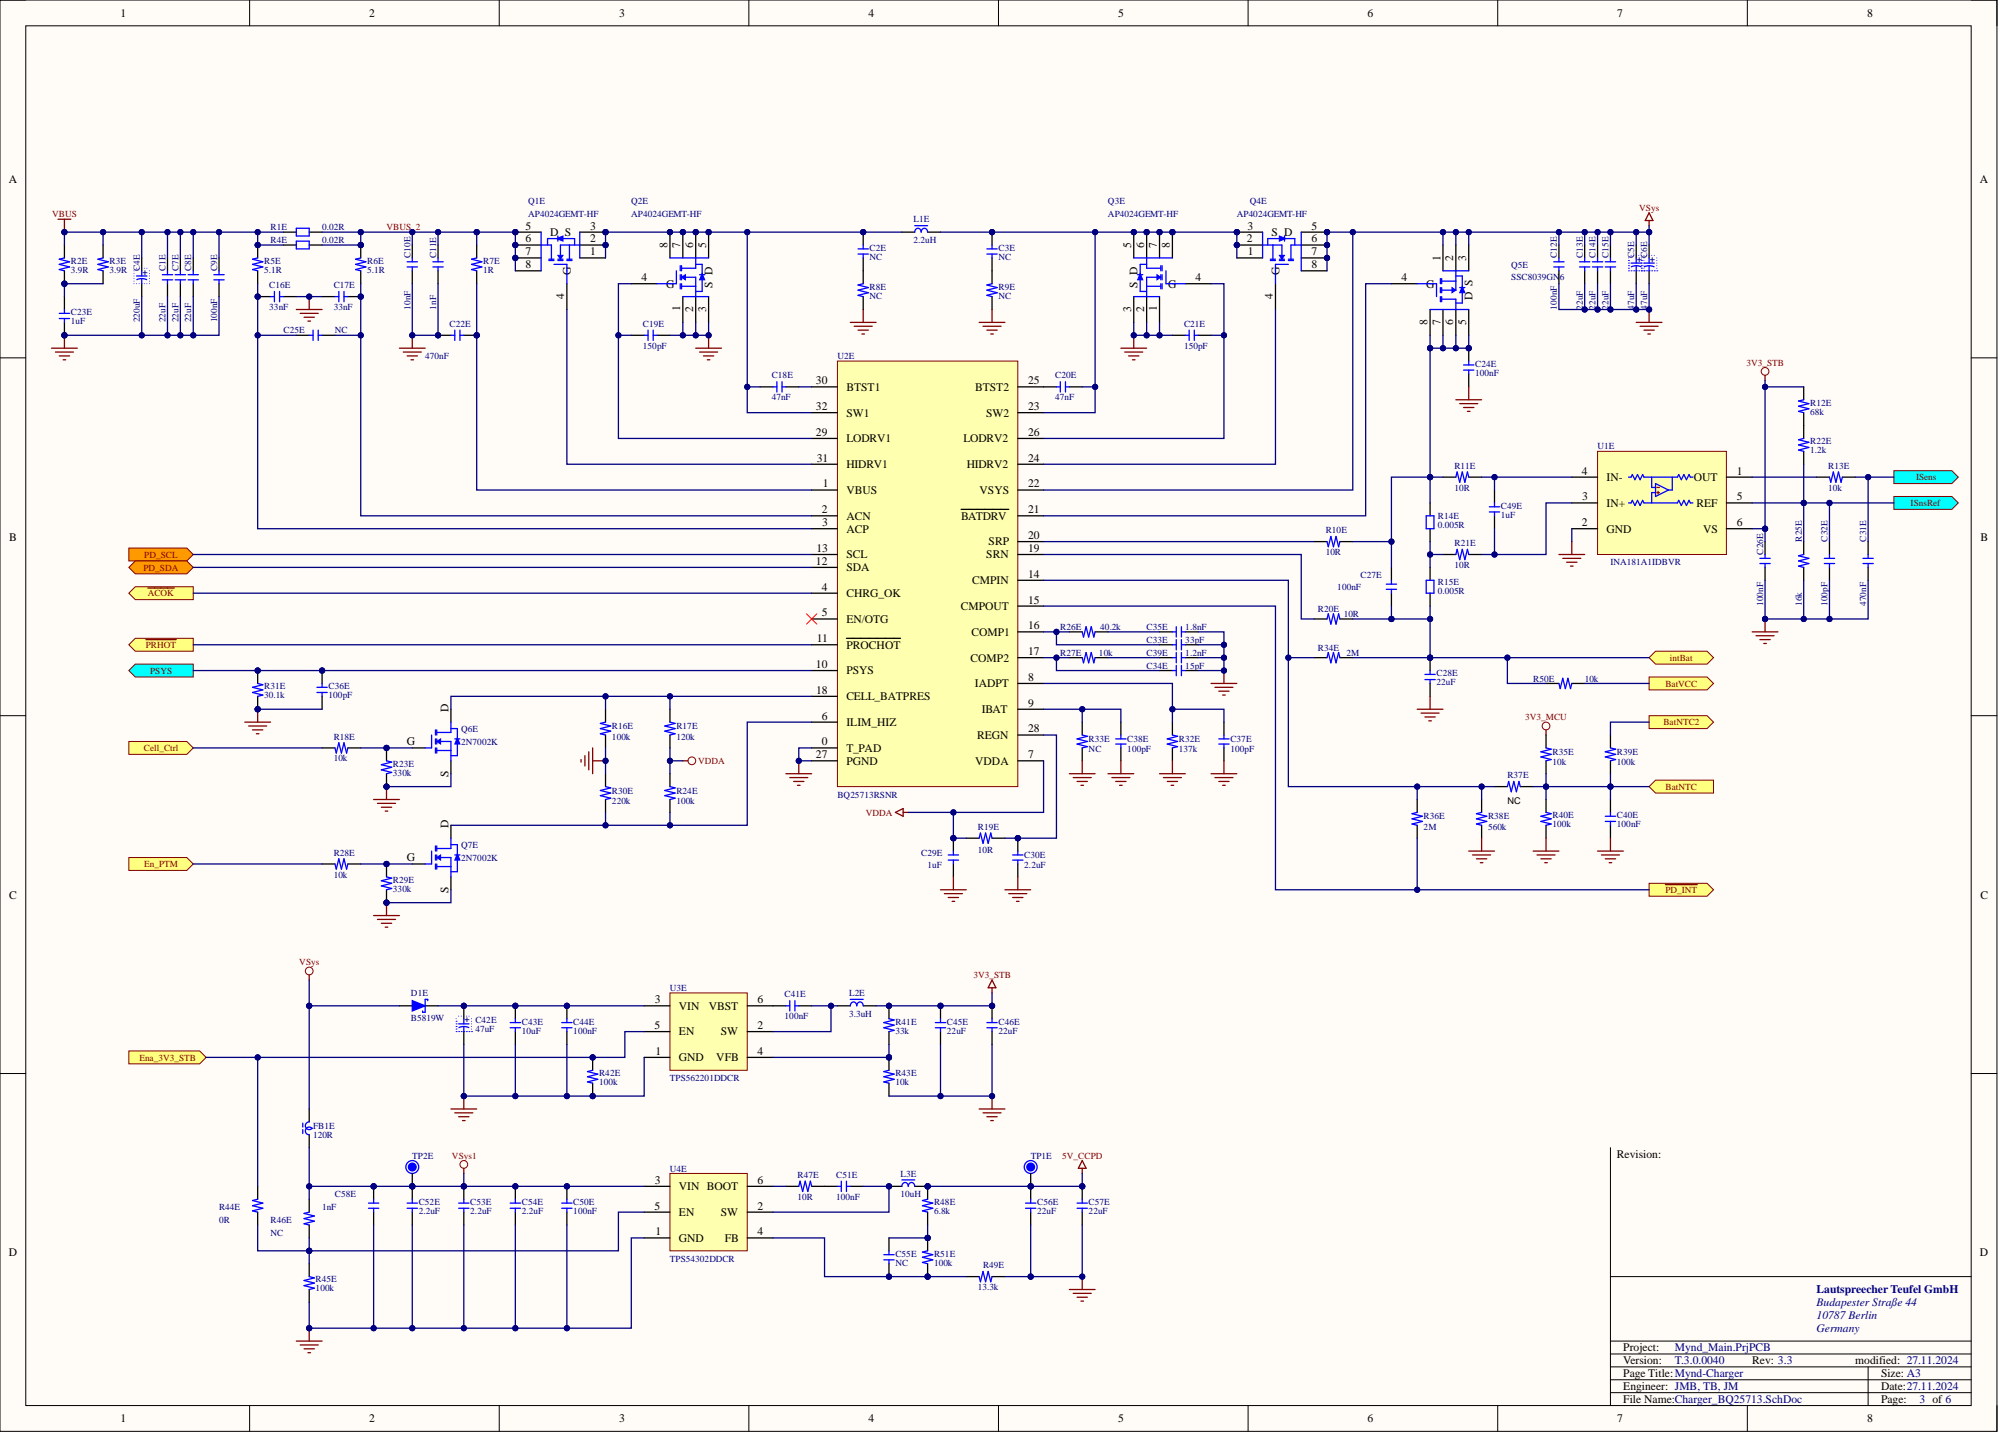
[picture p63: page 3]

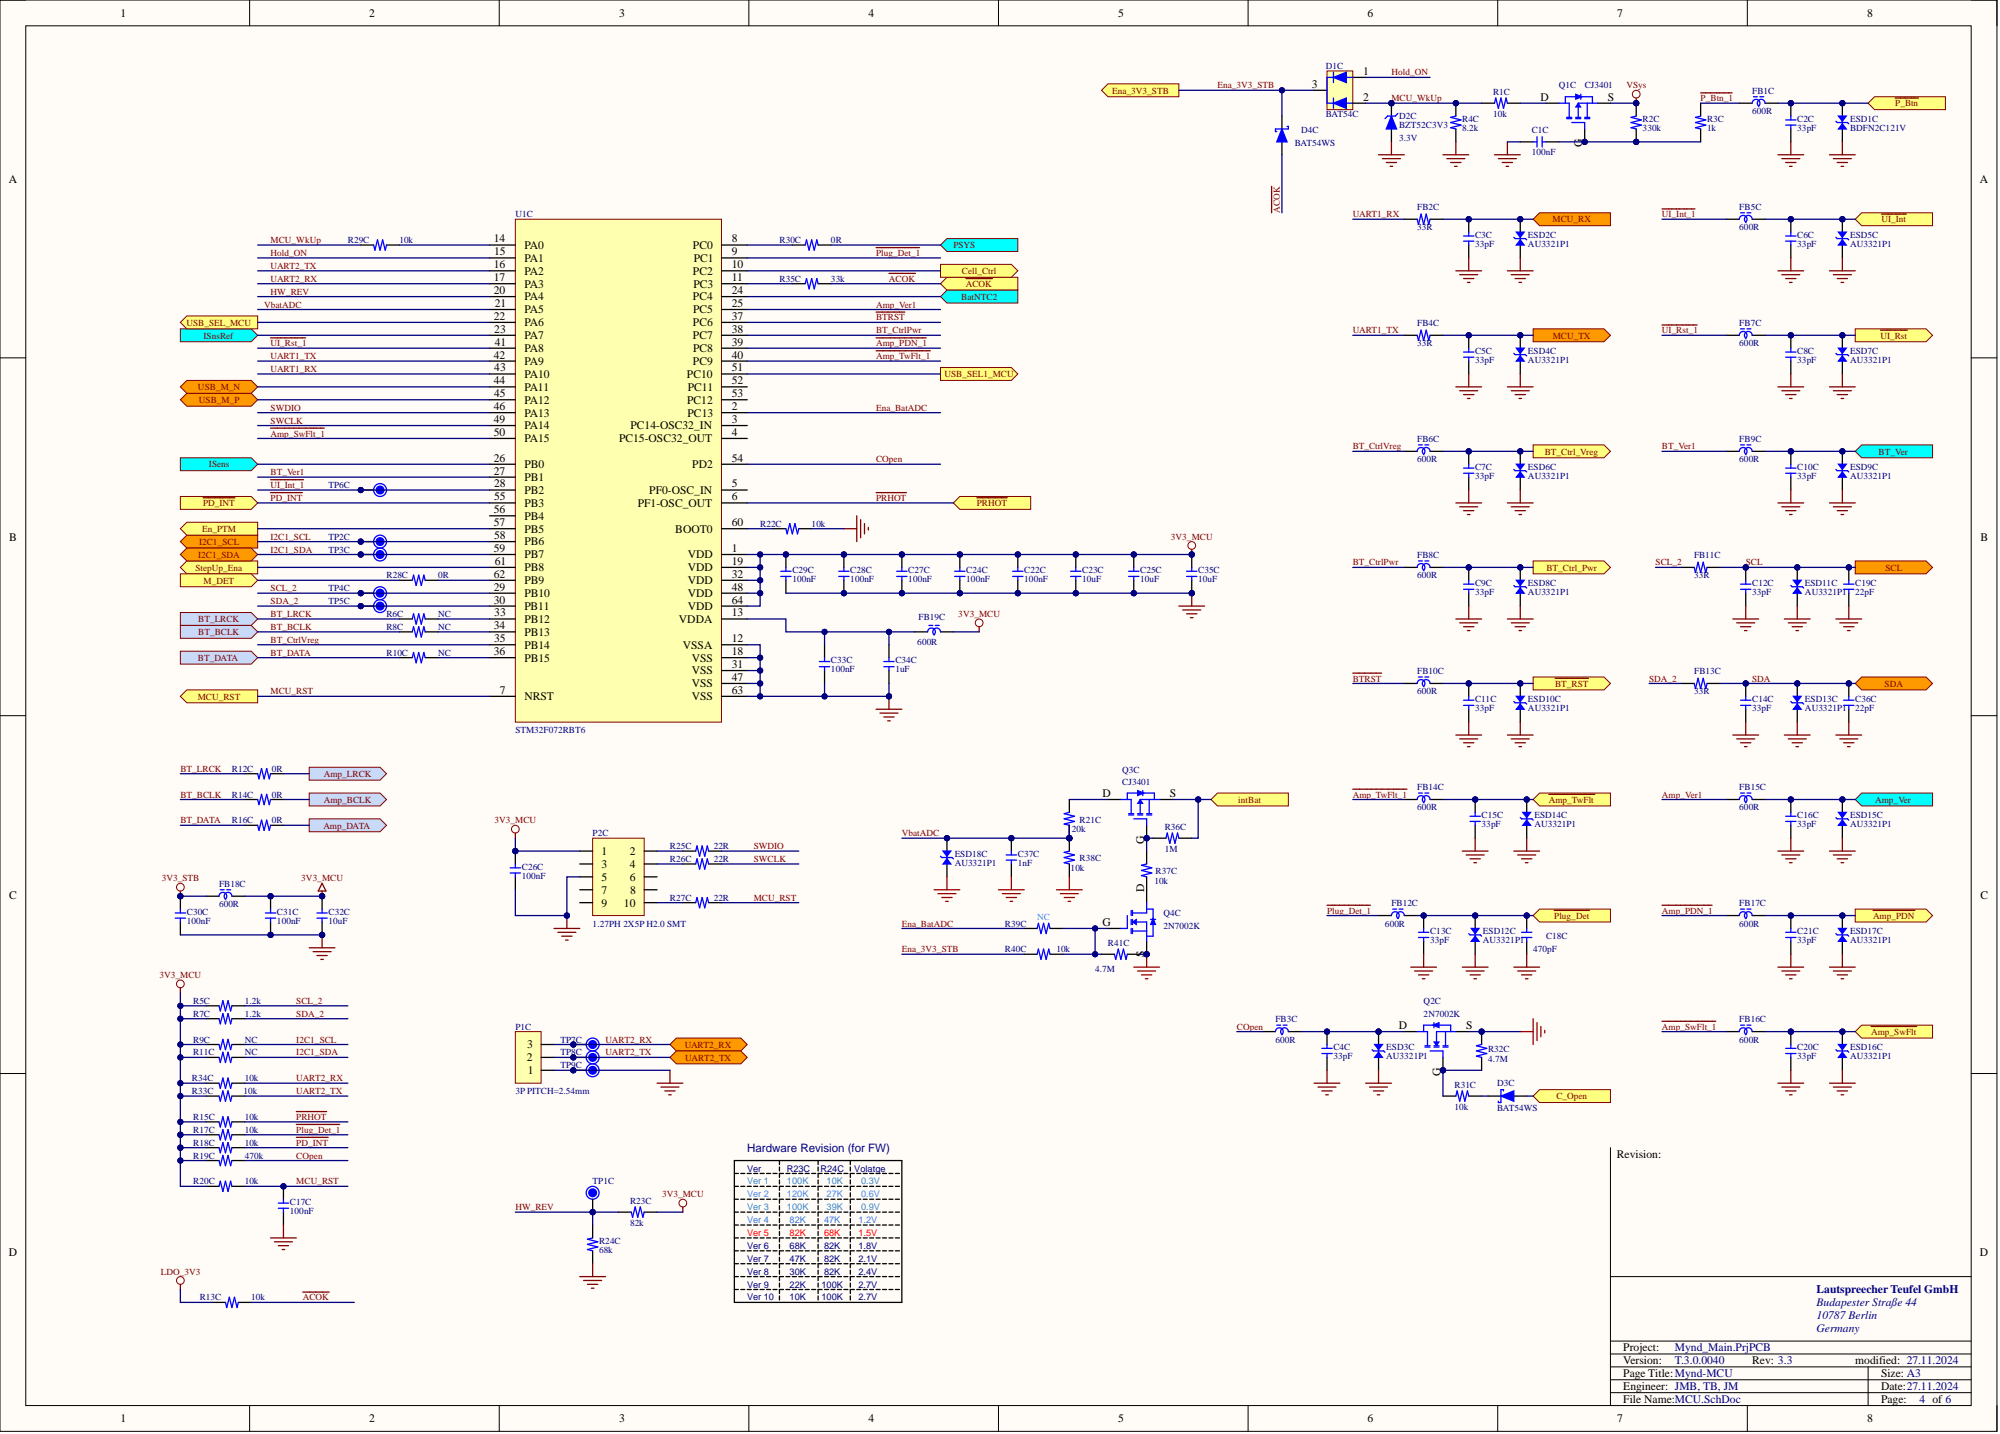
[picture p64: page 4]

Hardware Revision (for FW)

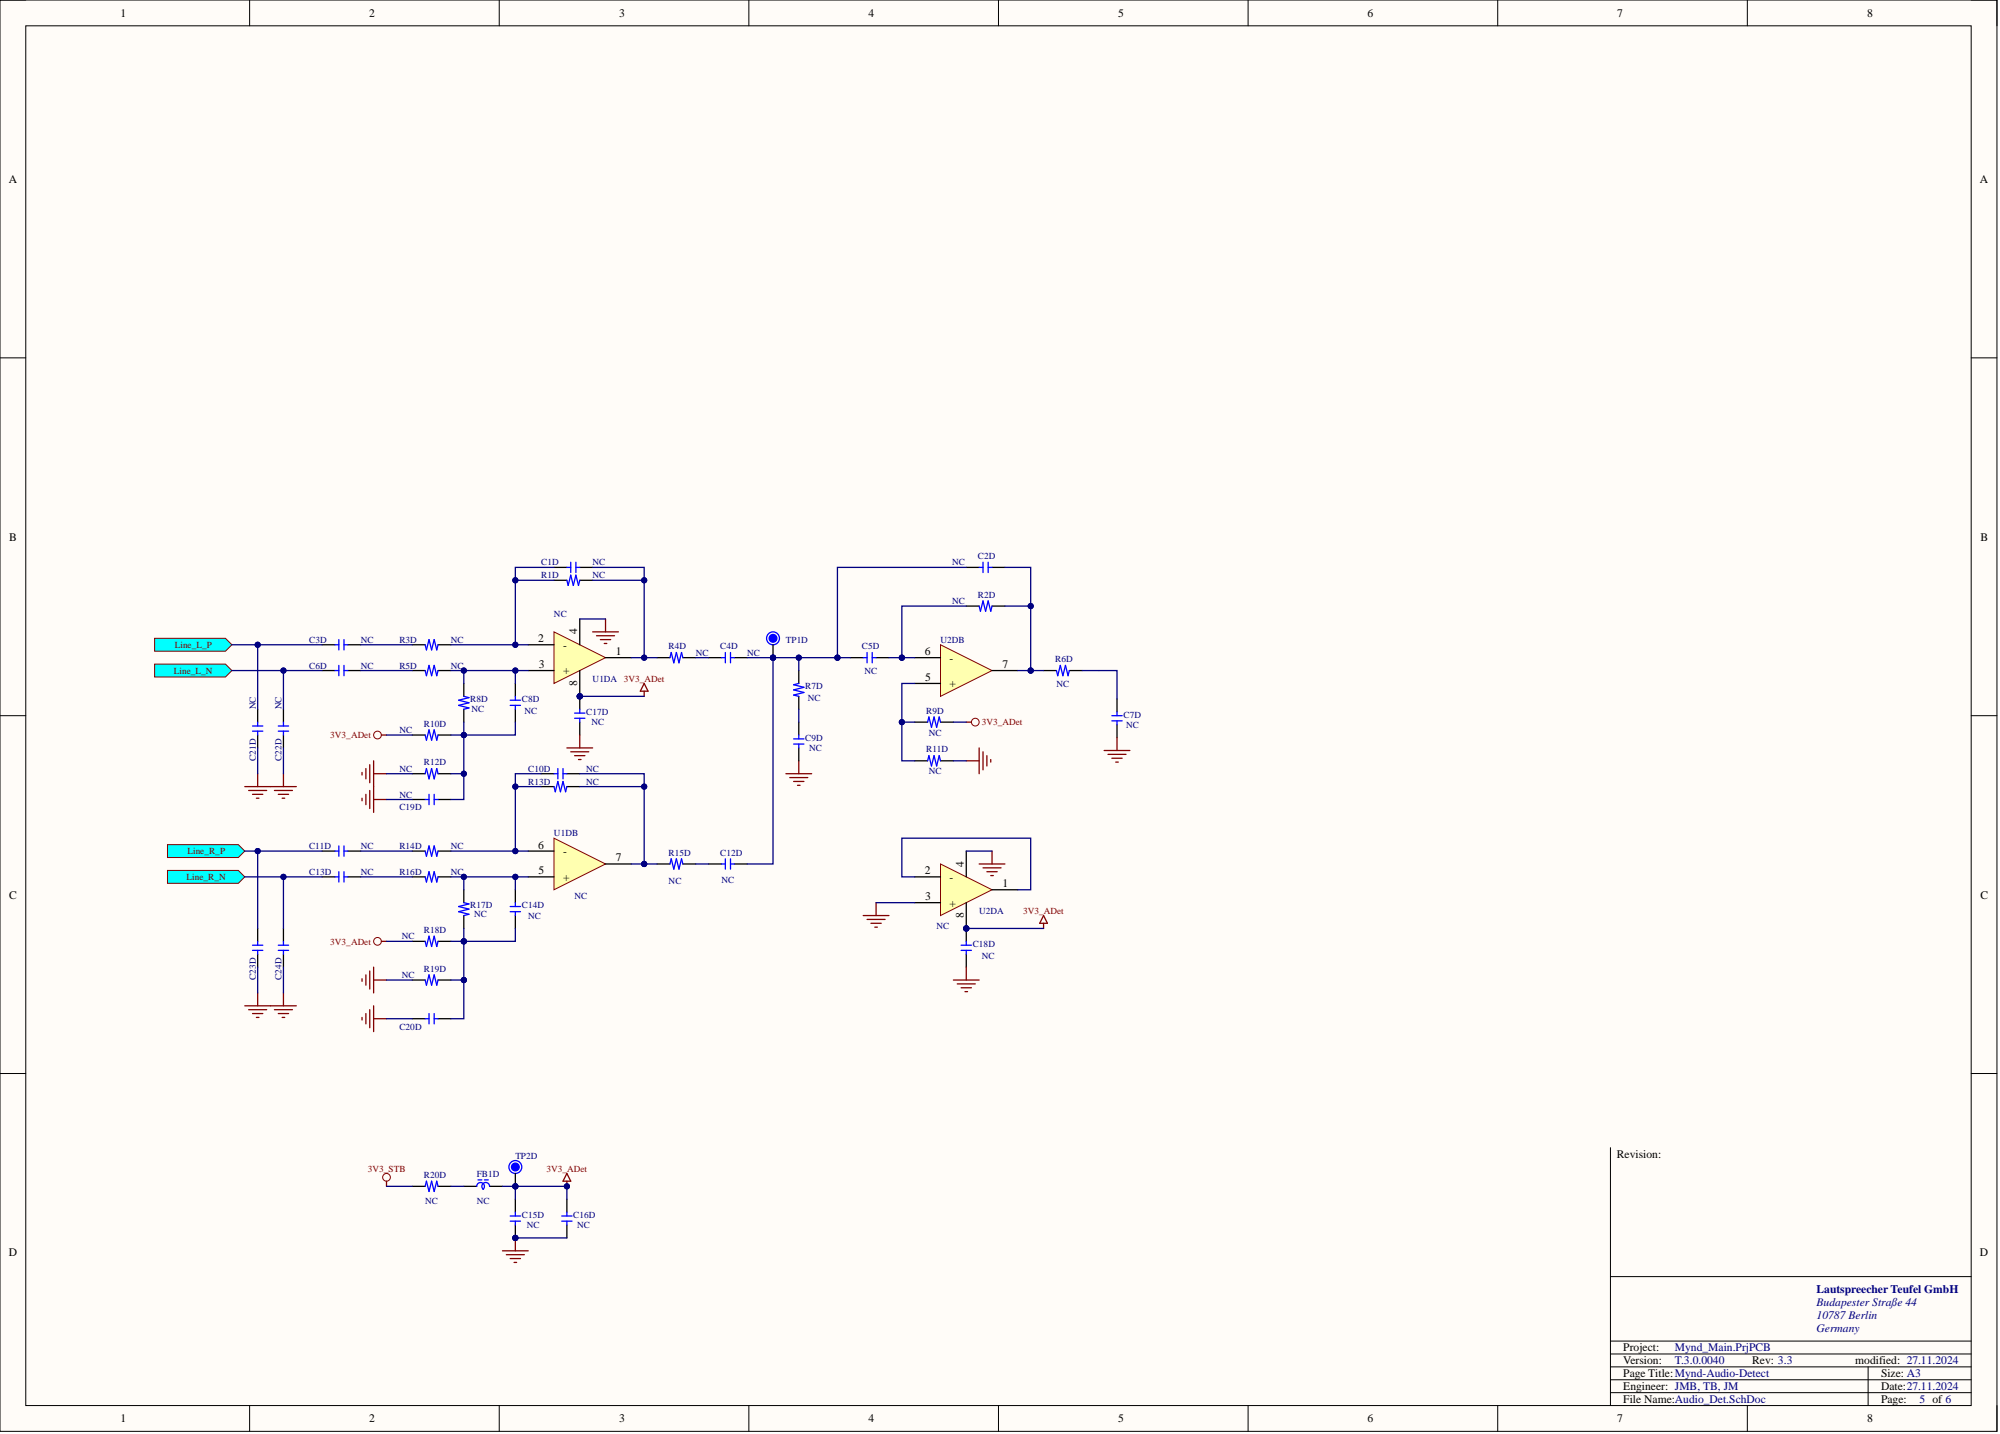
[picture p65: page 5]

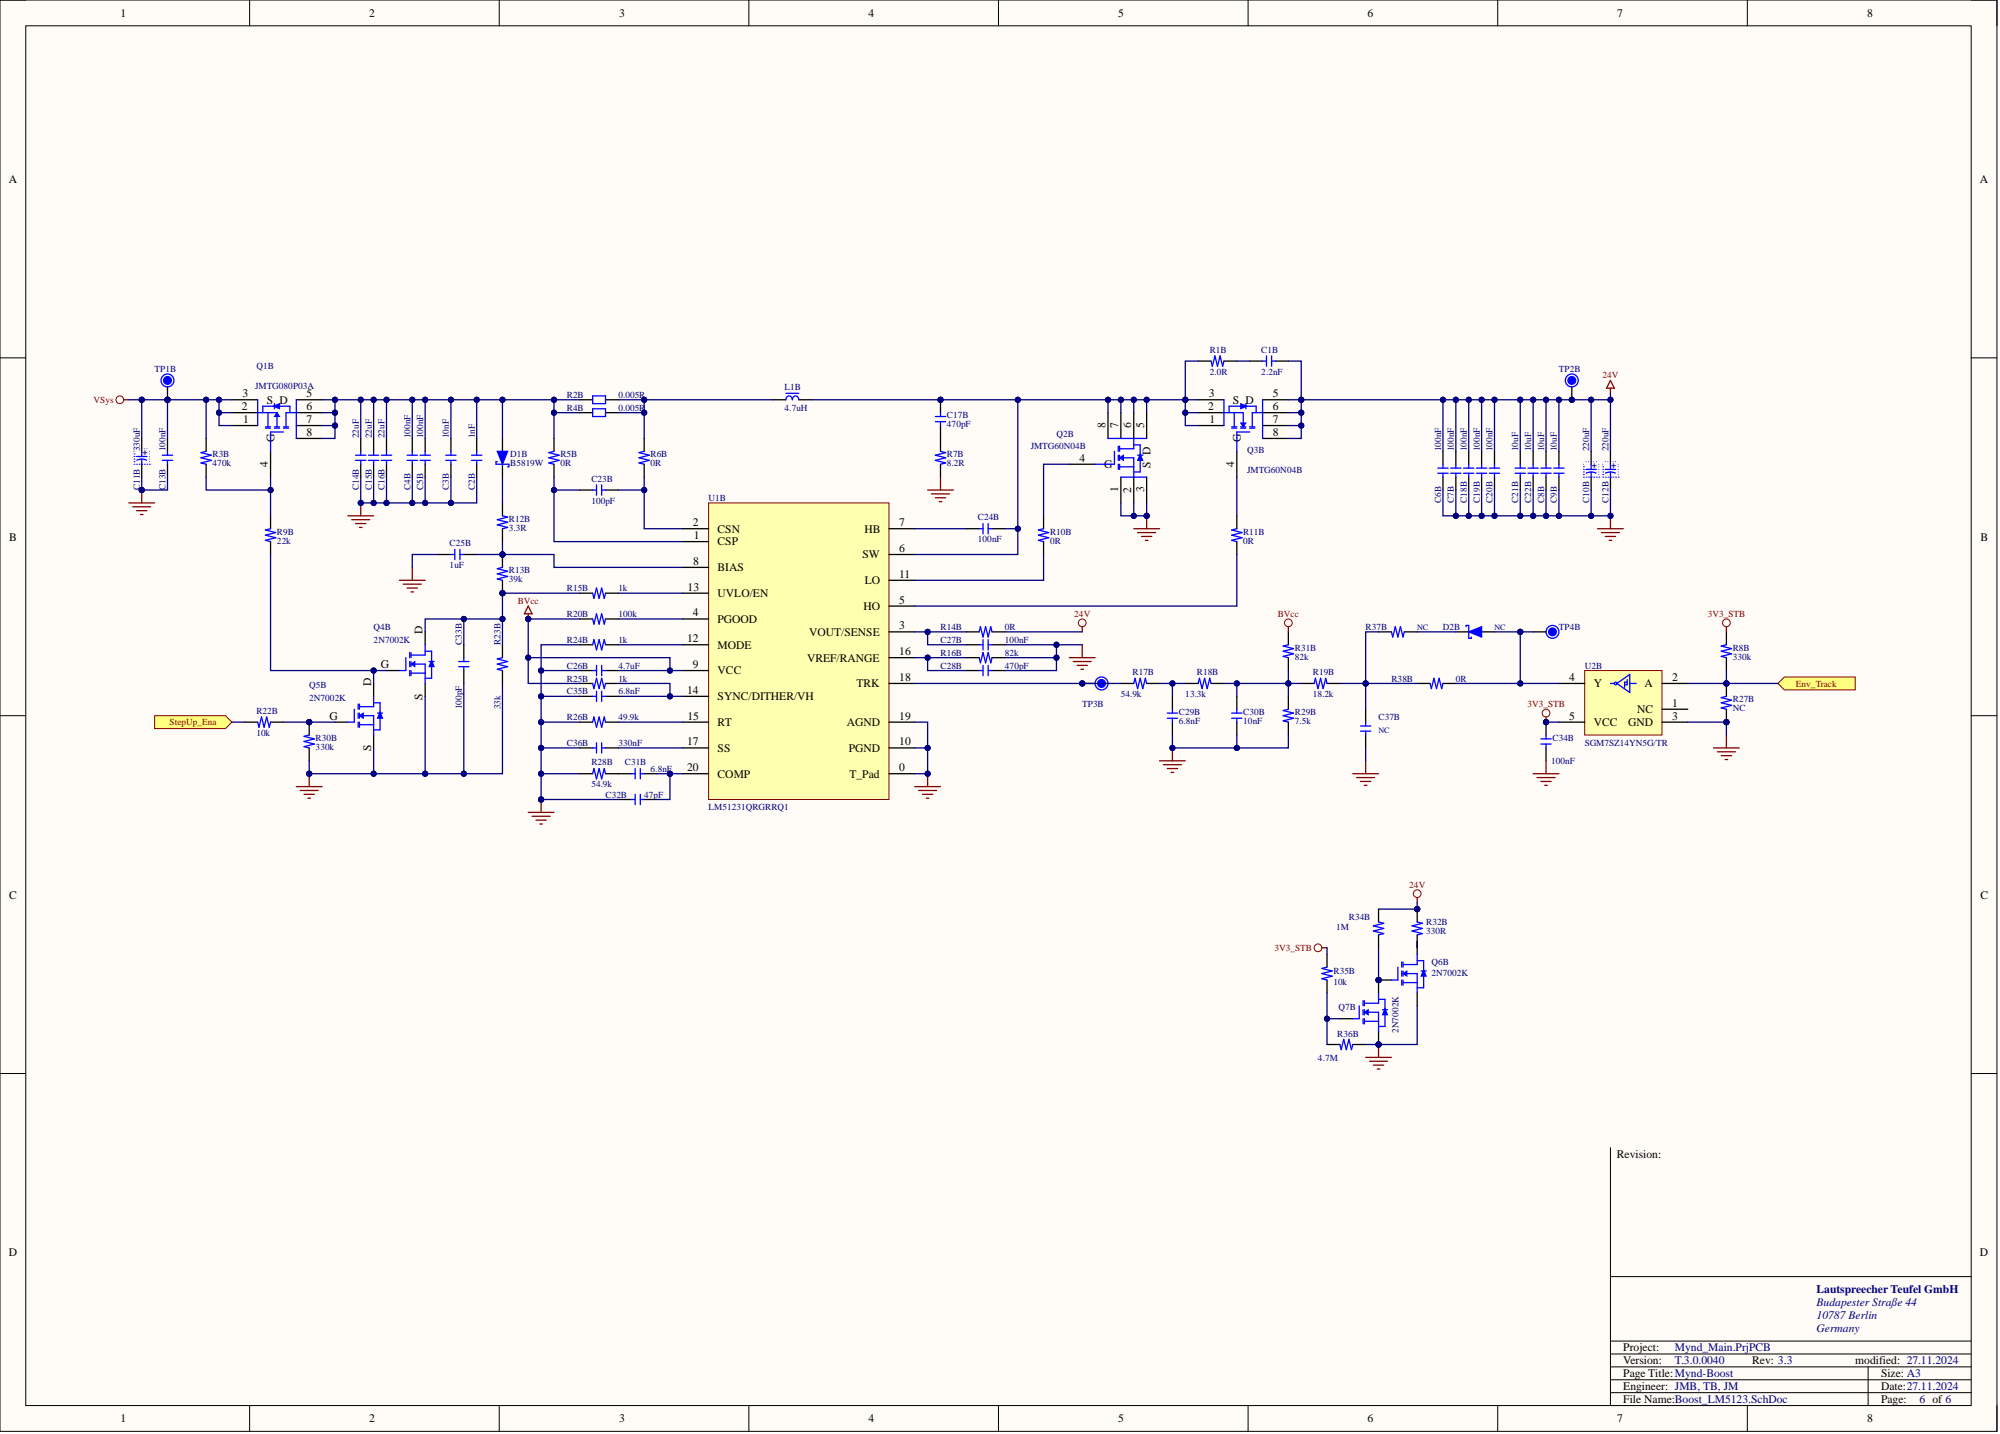
[picture p66: page 6]

R24B 1k | | MODE 12

VCC 9 | R16B | 82k
