teufelaudio/mynd-hardware/PCB_Schematics/PDF/Mynd_UI_SCH.PDF

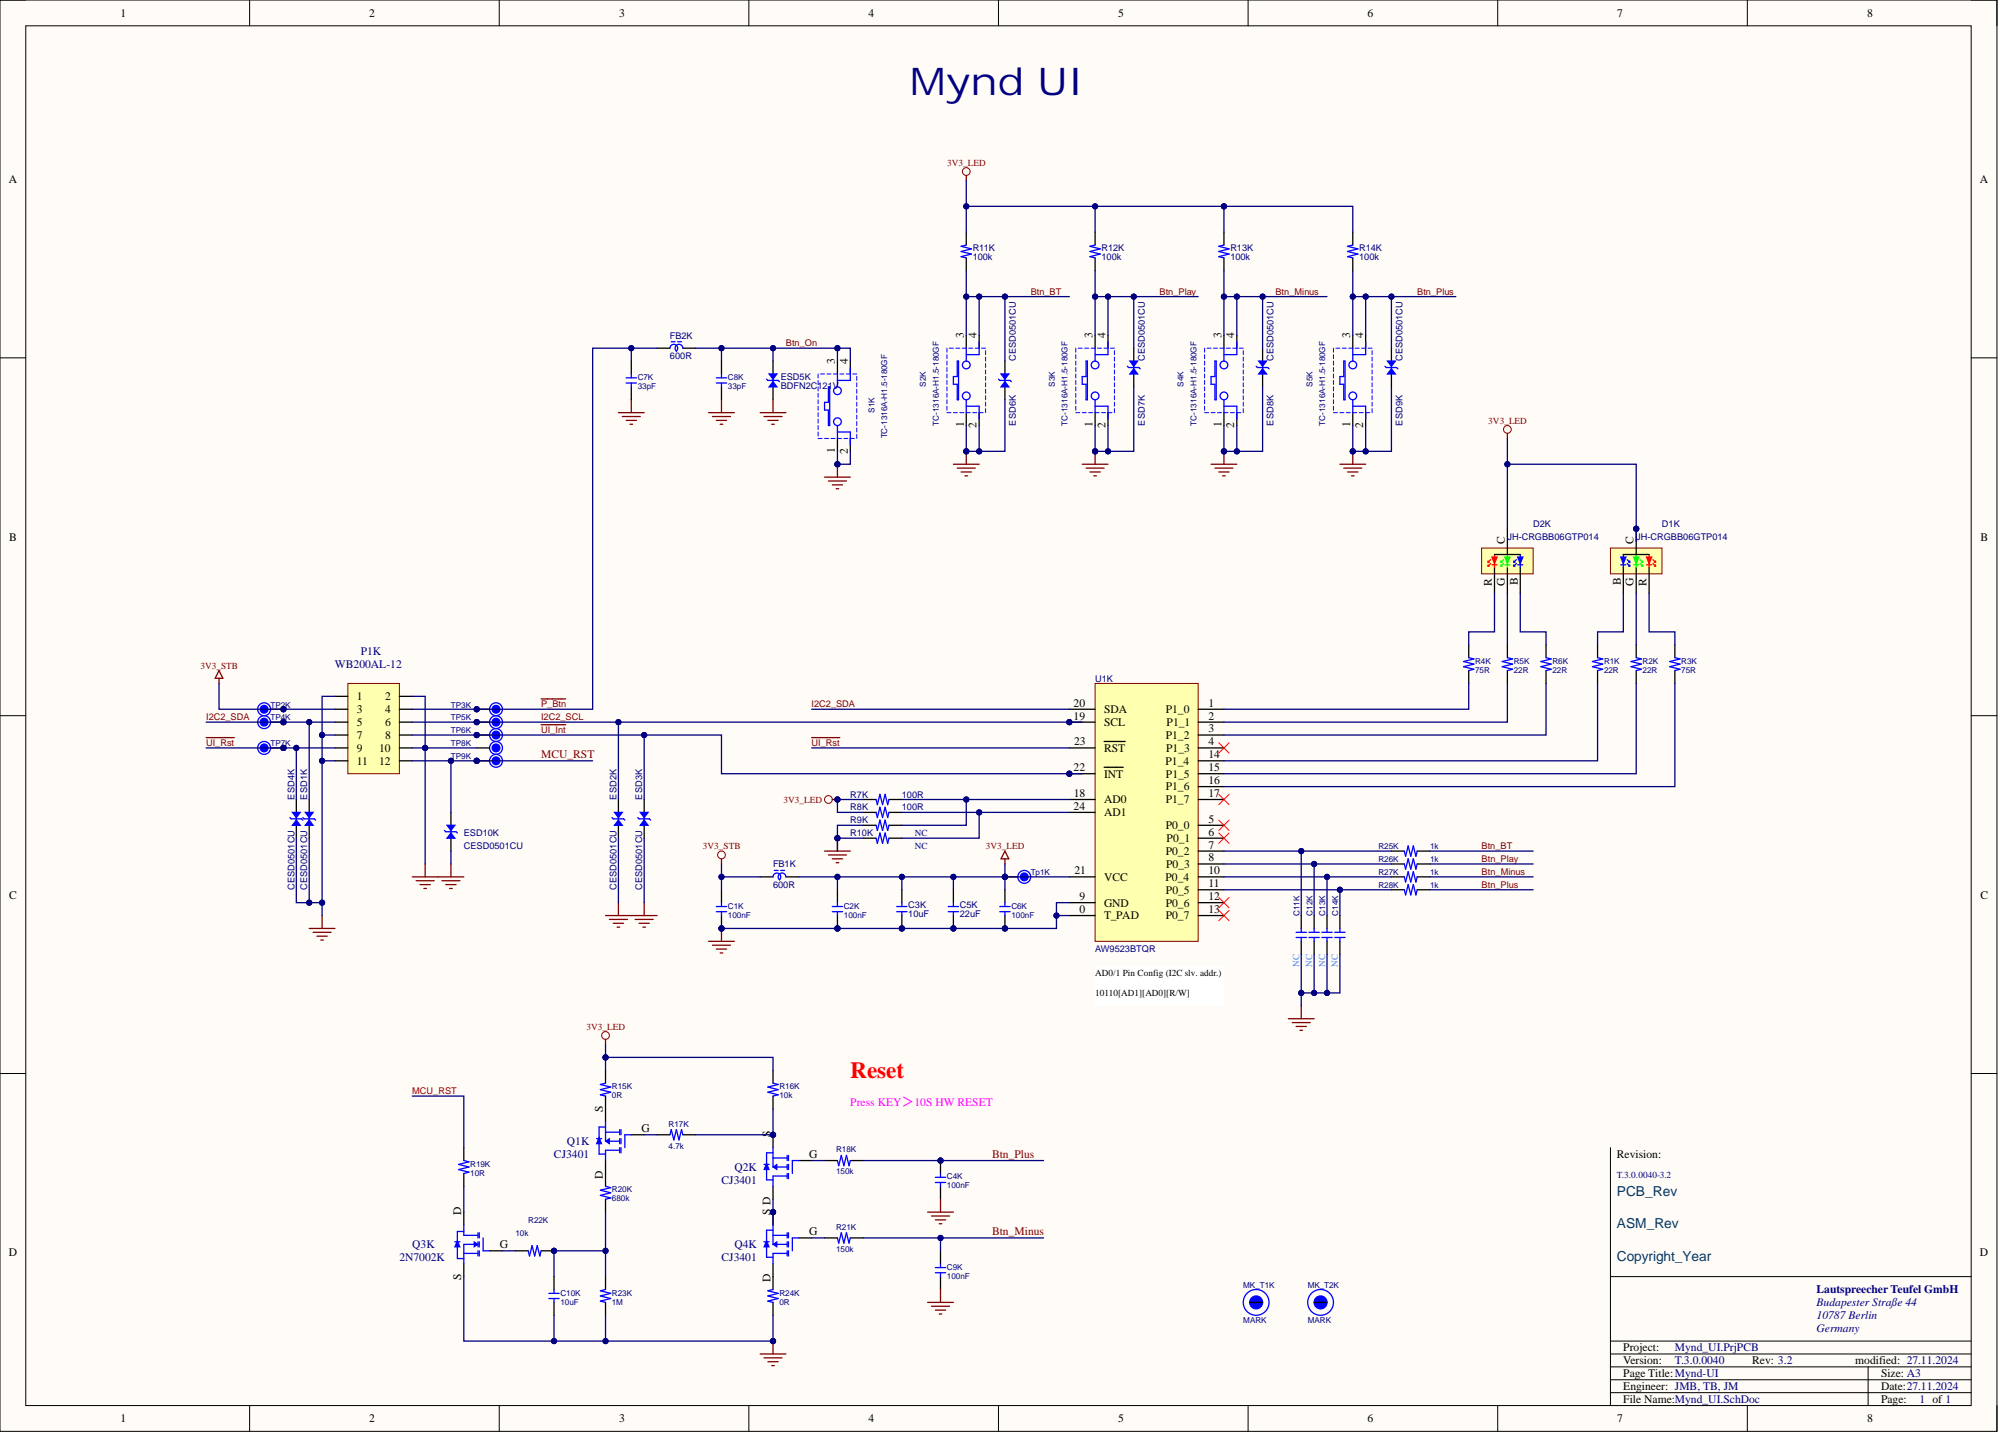
[picture p67: page 1]

AD0/1 Pin Config (I2C slv. addr.)

Press KEY＞10S HW RESET
