teufelaudio/mynd-hardware/PCB_Schematics/PDF/Mynd_Line_IN_Jack_SCH.PDF

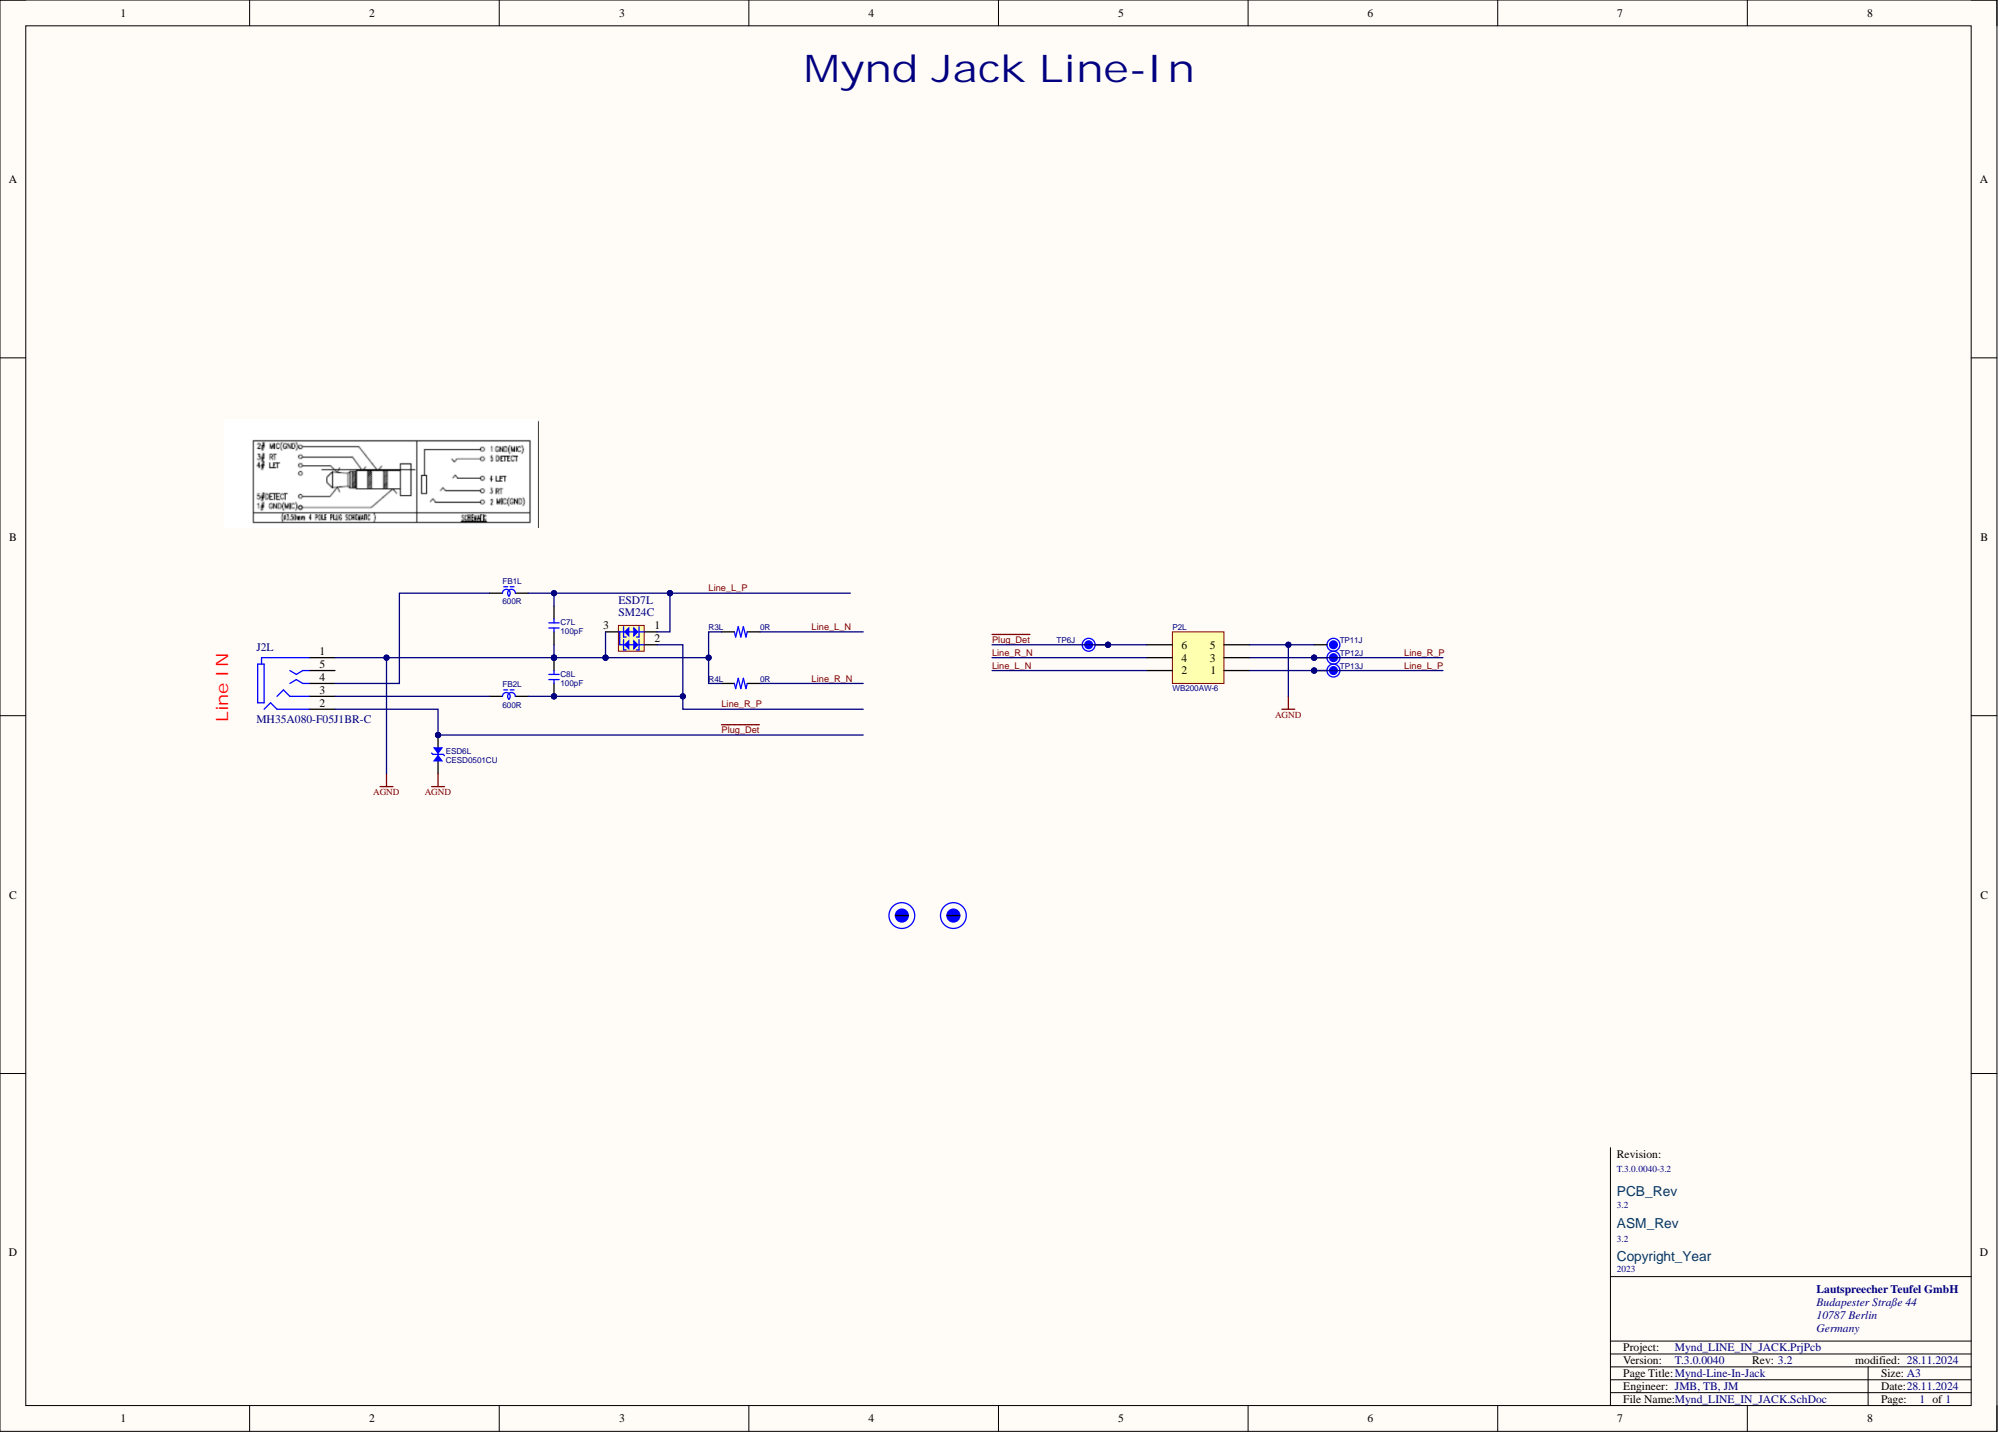
[picture p85: page 1]

Mynd Jack Line-In

Mynd-Line-In-Jack
JMB, TB, JM
Mynd_LINE_IN_JACK.SchDoc
