teufelaudio/mynd-hardware/PCB_Schematics/PDF/Mynd_Main_Assy.PDF

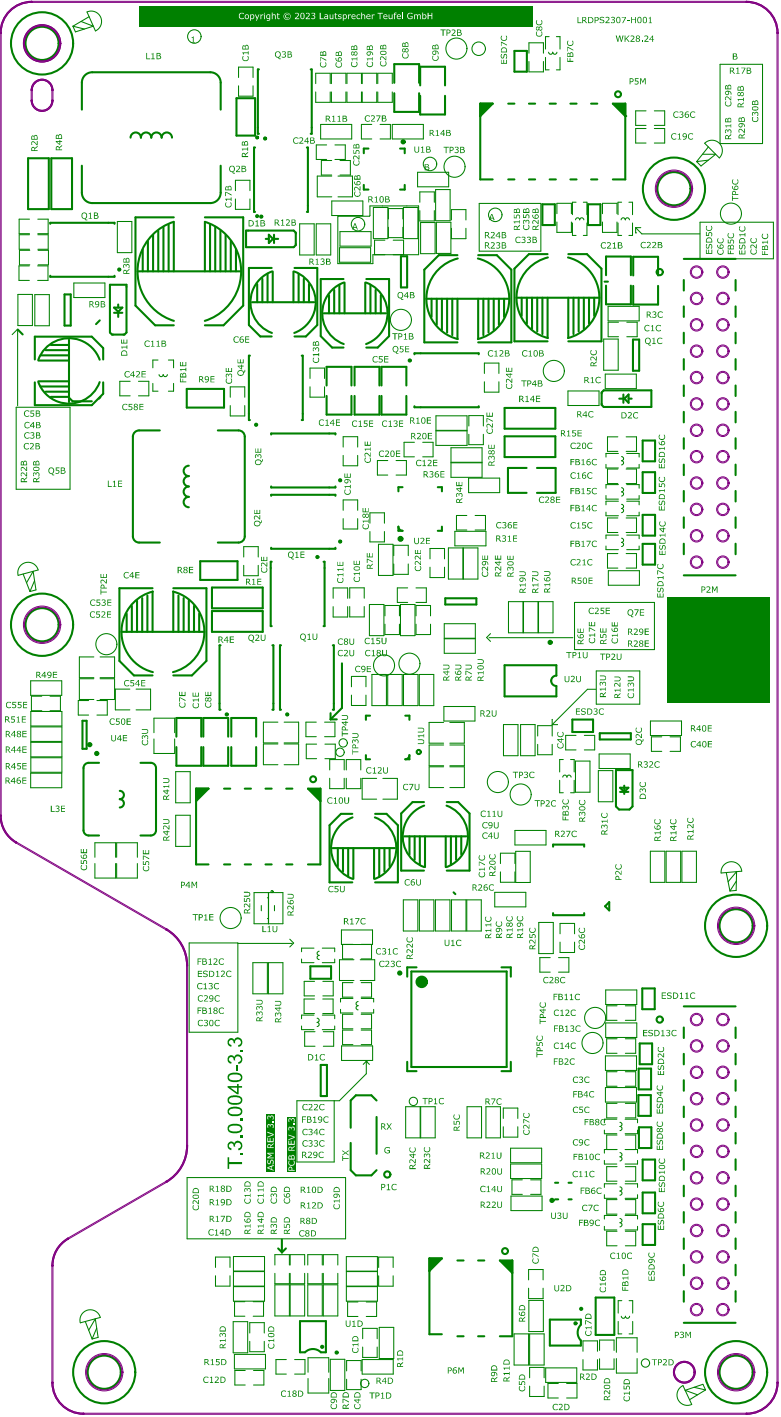
[picture p86: page 1]

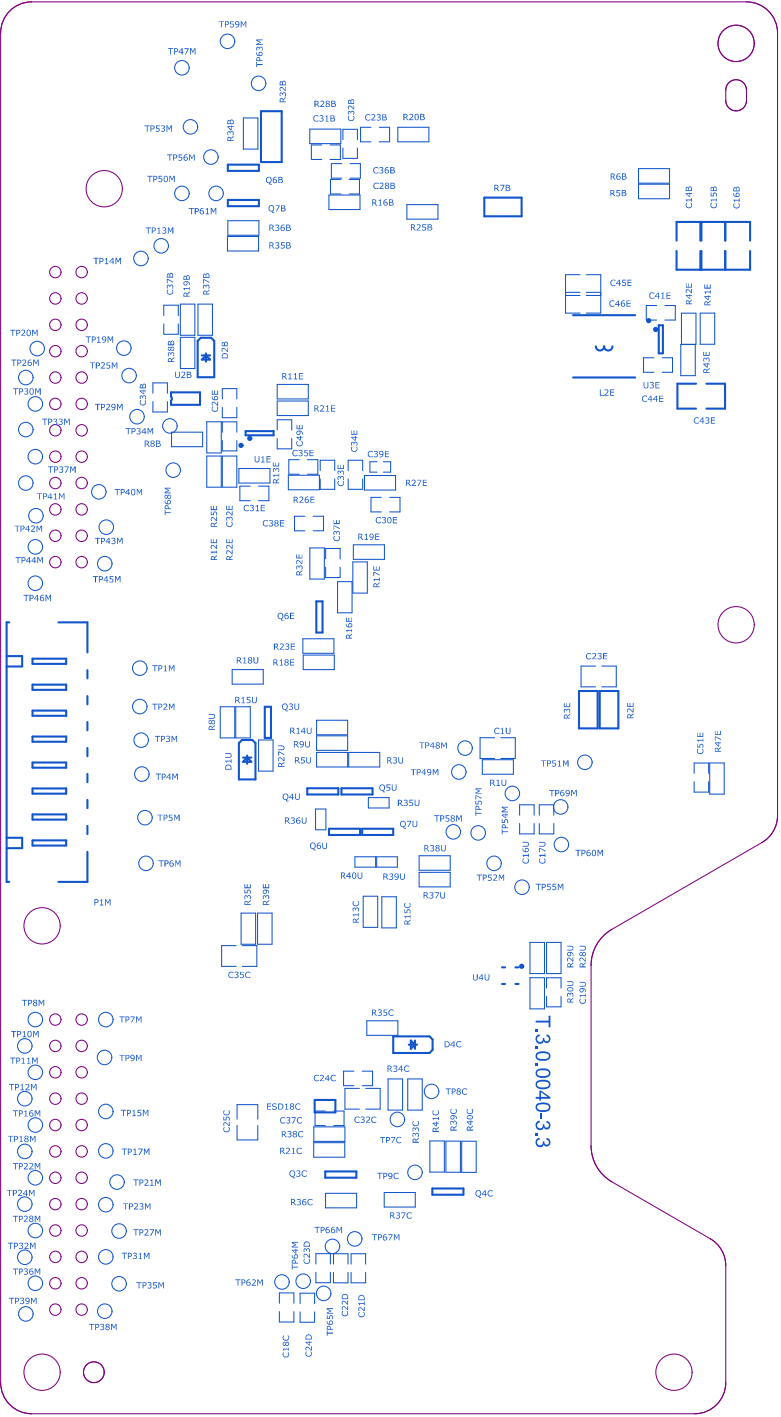
[picture p87: page 2]
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
