teufelaudio/mynd-hardware/PCB_Schematics/PDF/Mynd_UI_Assy.PDF

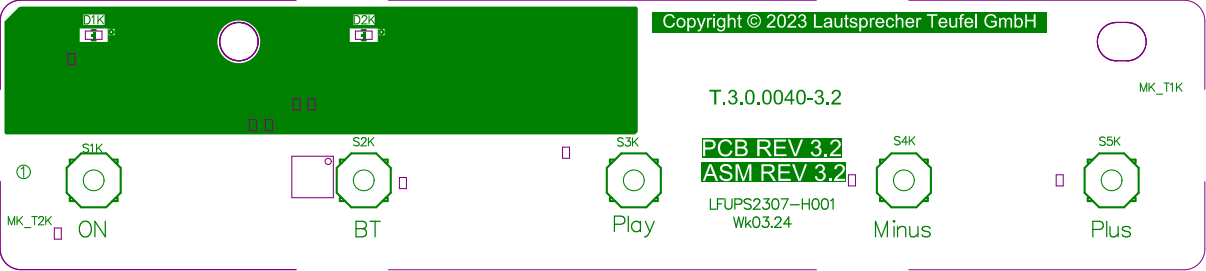
[picture p88: page 1]

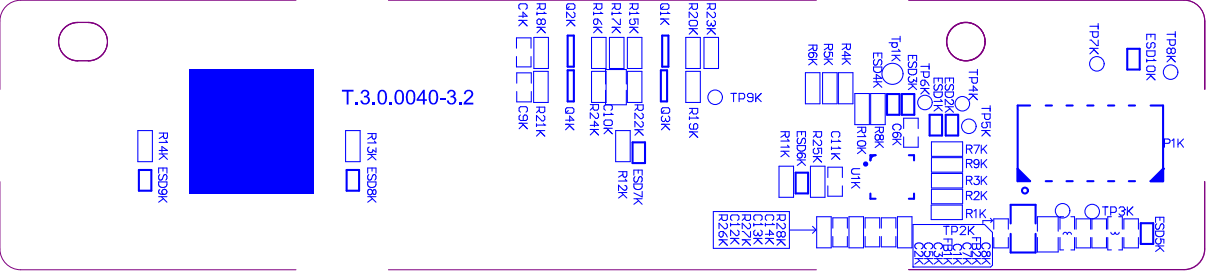
[picture p89: page 2]
