teufelaudio/mynd-hardware/PCB_Schematics/PDF/Mynd_USB_Jack_Assy.PDF

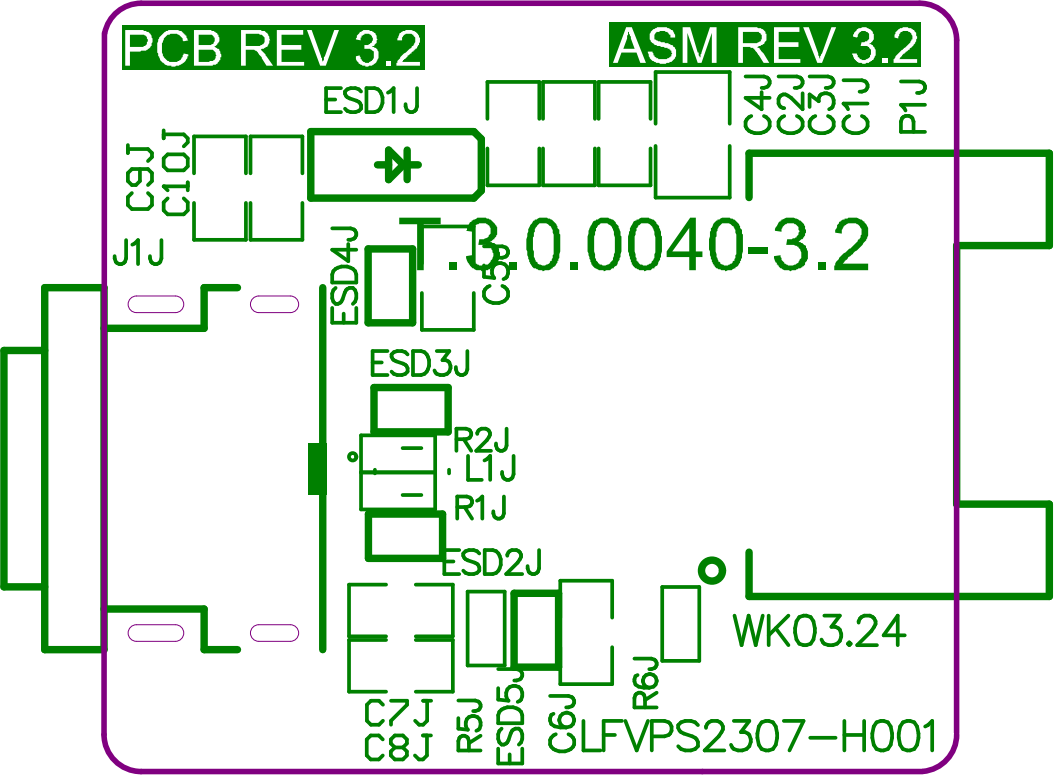
[picture p90: page 1]

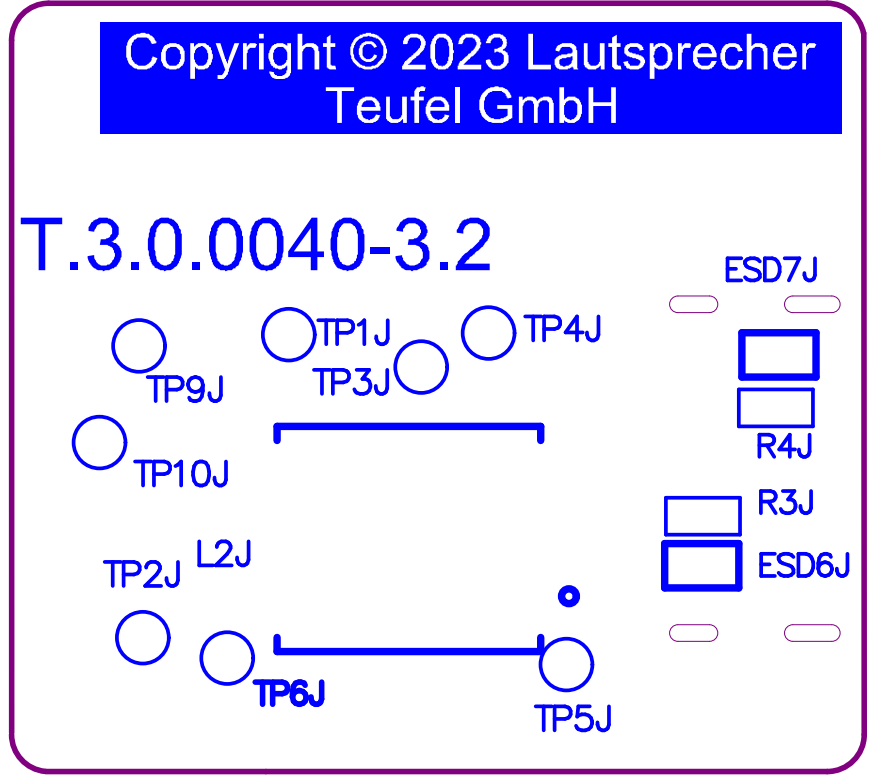
[picture p91: page 2]
