teufelaudio/mynd-hardware/PCB_Schematics/PDF/Mynd_USB_Jack_SCH.PDF

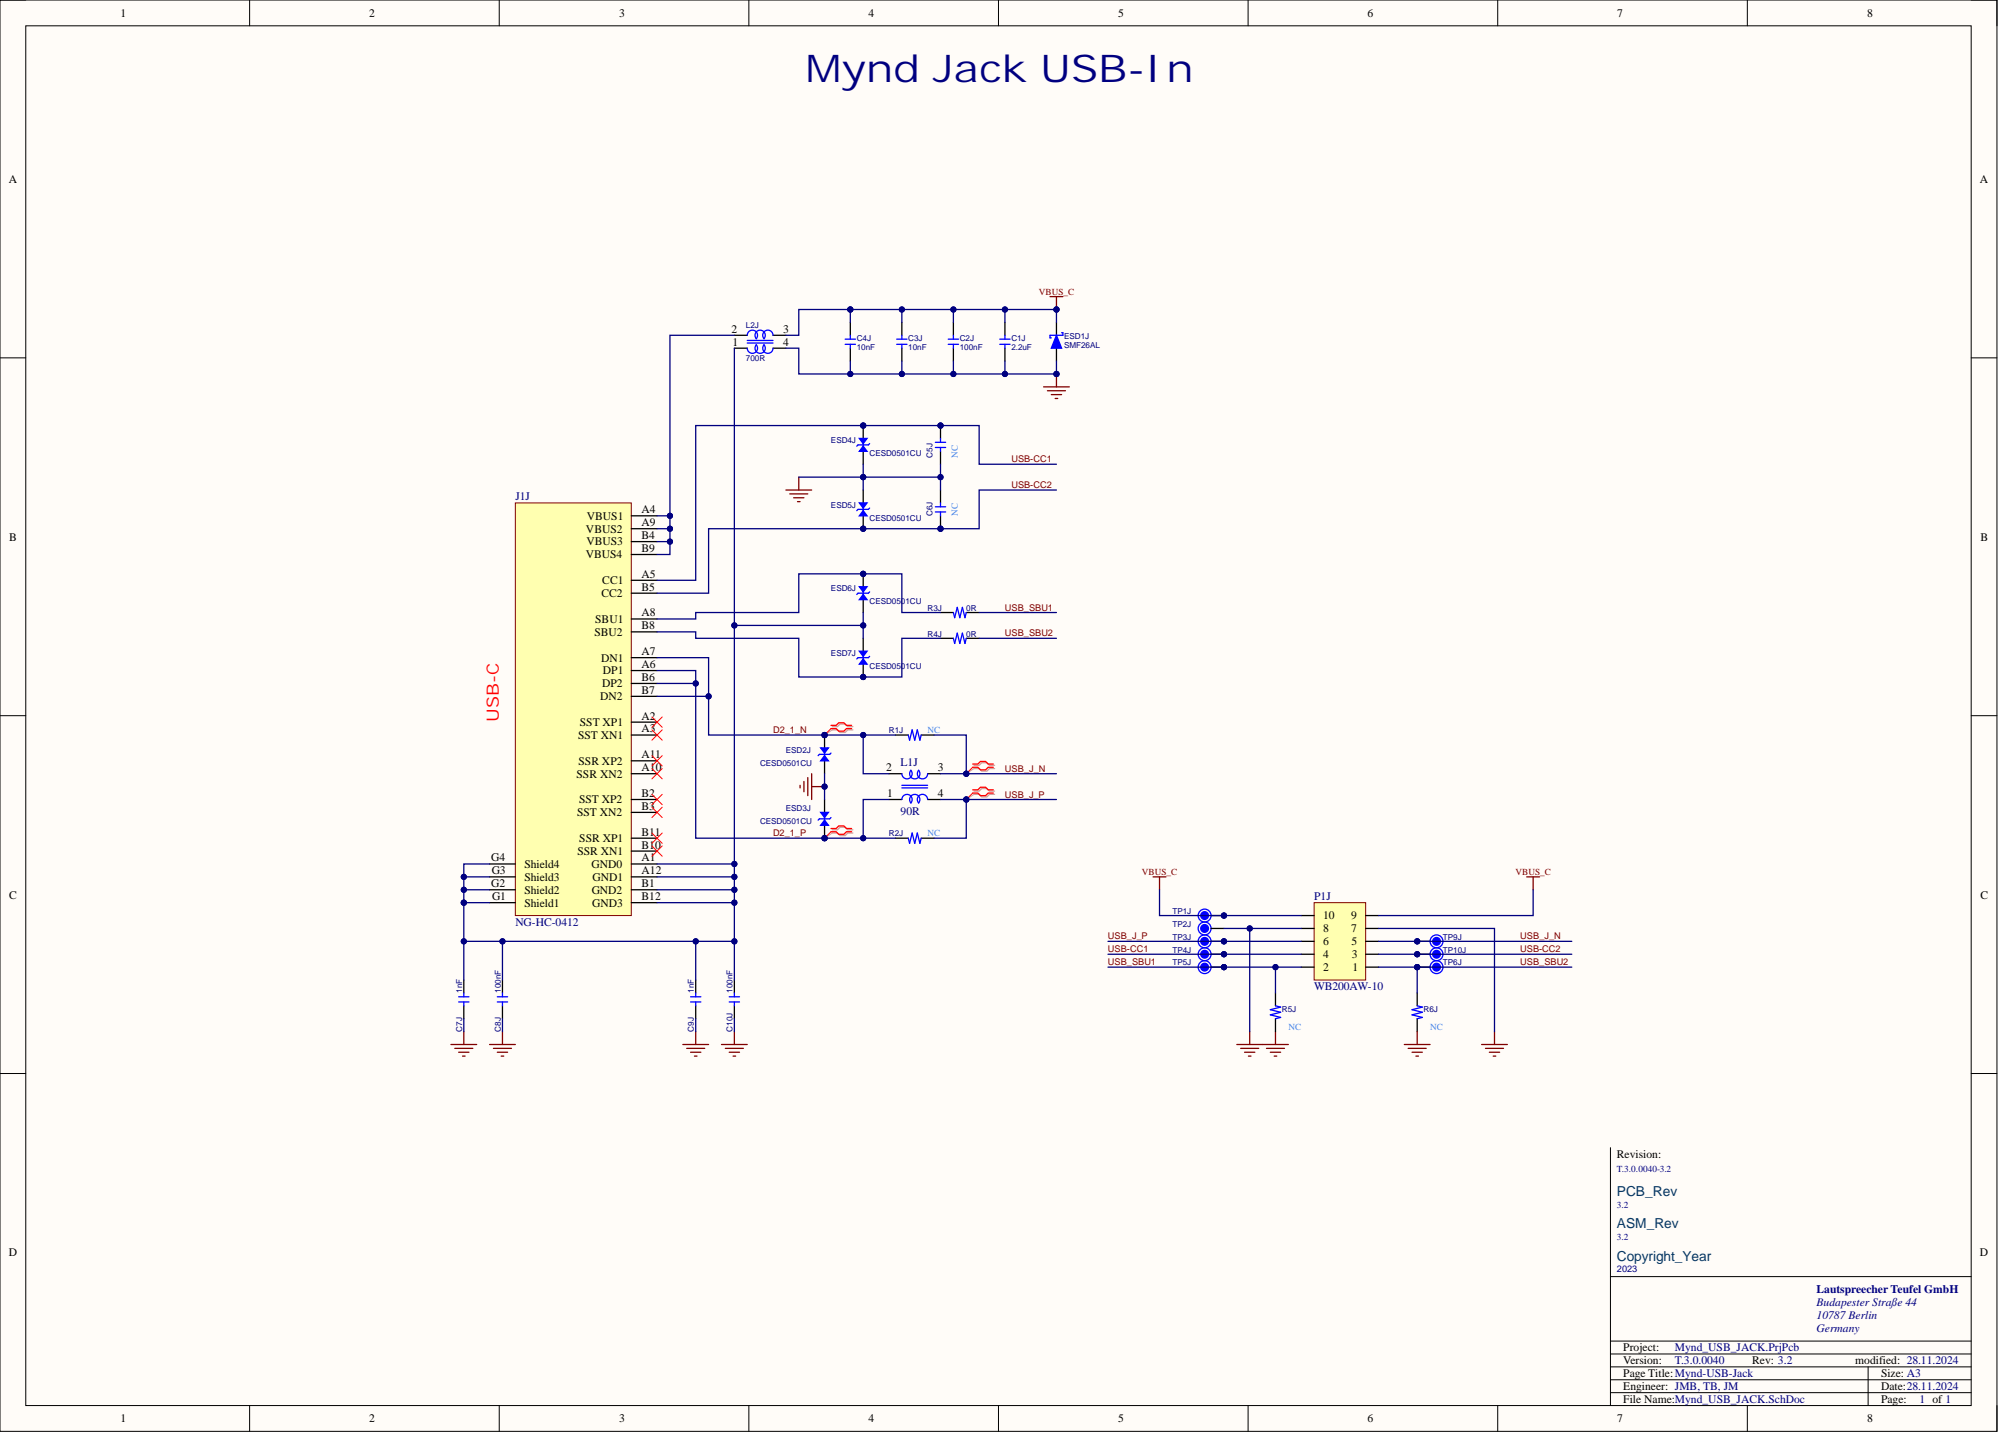
[picture p92: page 1]

Mynd Jack USB-In
